bestlaohe/newmsg/Peripheral/inc/ch32v00x.h

/********************************** (C) COPYRIGHT  *******************************
 * File Name          : ch32v00x.h
 * Author             : WCH
 * Version            : V1.0.0
 * Date               : 2024/05/28
 * Description        : CH32V00x Device Peripheral Access Layer Header File.
 *********************************************************************************
 * Copyright (c) 2021 Nanjing Qinheng Microelectronics Co., Ltd.
 * Attention: This software (modified or not) and binary are used for 
 * microcontroller manufactured by Nanjing Qinheng Microelectronics.
 *******************************************************************************/
#ifndef __CH32V00x_H
#define __CH32V00x_H

#ifdef __cplusplus
extern "C" {
#endif

#define HSE_VALUE                 ((uint32_t)24000000) /* Value of the External oscillator in Hz */

/* In the following line adjust the External High Speed oscillator (HSE) Startup Timeout value */
#define HSE_STARTUP_TIMEOUT       ((uint16_t)0x2000) /* Time out for HSE start up */

#define HSI_VALUE                 ((uint32_t)24000000) /* Value of the Internal oscillator in Hz */

/* CH32V00x Standard Peripheral Library version number */
#define __CH32V00x_STDPERIPH_VERSION_MAIN   (0x01) /* [15:8] main version */
#define __CH32V00x_STDPERIPH_VERSION_SUB    (0x09) /* [7:0] sub version */
#define __CH32V00x_STDPERIPH_VERSION        ( (__CH32V00x_STDPERIPH_VERSION_MAIN << 8)\
                                             |(__CH32V00x_STDPERIPH_VERSION_SUB << 0))

/* Interrupt Number Definition, according to the selected device */
typedef enum IRQn
{
    /******  RISC-V Processor Exceptions Numbers *******************************************************/
    NonMaskableInt_IRQn = 2, /* 2 Non Maskable Interrupt                             */
    EXC_IRQn = 3,            /* 3 Exception Interrupt                                */
    SysTicK_IRQn = 12,       /* 12 System timer Interrupt                            */
    Software_IRQn = 14,      /* 14 software Interrupt                                */

    /******  RISC-V specific Interrupt Numbers *********************************************************/
    WWDG_IRQn = 16,          /* Window WatchDog Interrupt                            */
    PVD_IRQn = 17,           /* PVD through EXTI Line detection Interrupt            */
    FLASH_IRQn = 18,         /* FLASH global Interrupt                               */
    RCC_IRQn = 19,           /* RCC global Interrupt                                 */
    EXTI7_0_IRQn = 20,       /* External Line[7:0] Interrupts                        */
    AWU_IRQn = 21,           /* AWU global Interrupt                                 */
    DMA1_Channel1_IRQn = 22, /* DMA1 Channel 1 global Interrupt                      */
    DMA1_Channel2_IRQn = 23, /* DMA1 Channel 2 global Interrupt                      */
    DMA1_Channel3_IRQn = 24, /* DMA1 Channel 3 global Interrupt                      */
    DMA1_Channel4_IRQn = 25, /* DMA1 Channel 4 global Interrupt                      */
    DMA1_Channel5_IRQn = 26, /* DMA1 Channel 5 global Interrupt                      */
    DMA1_Channel6_IRQn = 27, /* DMA1 Channel 6 global Interrupt                      */
    DMA1_Channel7_IRQn = 28, /* DMA1 Channel 7 global Interrupt                      */
    ADC_IRQn = 29,           /* ADC global Interrupt                                 */
    I2C1_EV_IRQn = 30,       /* I2C1 Event Interrupt                                 */
    I2C1_ER_IRQn = 31,       /* I2C1 Error Interrupt                                 */
    USART1_IRQn = 32,        /* USART1 global Interrupt                              */
    SPI1_IRQn = 33,          /* SPI1 global Interrupt                                */
    TIM1_BRK_IRQn = 34,      /* TIM1 Break Interrupt                                 */
    TIM1_UP_IRQn = 35,       /* TIM1 Update Interrupt                                */
    TIM1_TRG_COM_IRQn = 36,  /* TIM1 Trigger and Commutation Interrupt               */
    TIM1_CC_IRQn = 37,       /* TIM1 Capture Compare Interrupt                       */
    TIM2_IRQn = 38,          /* TIM2 global Interrupt                                */

} IRQn_Type;

#define HardFault_IRQn    EXC_IRQn

#include <stdint.h>
#include <core_riscv.h>
#include <system_ch32v00x.h>

/* Standard Peripheral Library old definitions (maintained for legacy purpose) */
#define HSI_Value             HSI_VALUE
#define HSE_Value             HSE_VALUE
#define HSEStartUp_TimeOut    HSE_STARTUP_TIMEOUT

/* Analog to Digital Converter */
typedef struct
{
    __IO uint32_t STATR;
    __IO uint32_t CTLR1;
    __IO uint32_t CTLR2;
    __IO uint32_t SAMPTR1;
    __IO uint32_t SAMPTR2;
    __IO uint32_t IOFR1;
    __IO uint32_t IOFR2;
    __IO uint32_t IOFR3;
    __IO uint32_t IOFR4;
    __IO uint32_t WDHTR;
    __IO uint32_t WDLTR;
    __IO uint32_t RSQR1;
    __IO uint32_t RSQR2;
    __IO uint32_t RSQR3;
    __IO uint32_t ISQR;
    __IO uint32_t IDATAR1;
    __IO uint32_t IDATAR2;
    __IO uint32_t IDATAR3;
    __IO uint32_t IDATAR4;
    __IO uint32_t RDATAR;
    __IO uint32_t DLYR;
} ADC_TypeDef;

/* Debug MCU */
typedef struct
{
    __IO uint32_t CFGR0;
    __IO uint32_t CFGR1;
} DBGMCU_TypeDef;

/* DMA Controller */
typedef struct
{
    __IO uint32_t CFGR;
    __IO uint32_t CNTR;
    __IO uint32_t PADDR;
    __IO uint32_t MADDR;
} DMA_Channel_TypeDef;

typedef struct
{
    __IO uint32_t INTFR;
    __IO uint32_t INTFCR;
} DMA_TypeDef;

/* External Interrupt/Event Controller */
typedef struct
{
    __IO uint32_t INTENR;
    __IO uint32_t EVENR;
    __IO uint32_t RTENR;
    __IO uint32_t FTENR;
    __IO uint32_t SWIEVR;
    __IO uint32_t INTFR;
} EXTI_TypeDef;

/* FLASH Registers */
typedef struct
{
    __IO uint32_t ACTLR;
    __IO uint32_t KEYR;
    __IO uint32_t OBKEYR;
    __IO uint32_t STATR;
    __IO uint32_t CTLR;
    __IO uint32_t ADDR;
    __IO uint32_t RESERVED;
    __IO uint32_t OBR;
    __IO uint32_t WPR;
    __IO uint32_t MODEKEYR;
    __IO uint32_t BOOT_MODEKEYR;
} FLASH_TypeDef;

/* Option Bytes Registers */
typedef struct
{
    __IO uint16_t RDPR;
    __IO uint16_t USER;
    __IO uint16_t Data0;
    __IO uint16_t Data1;
    __IO uint16_t WRPR0;
    __IO uint16_t WRPR1;
} OB_TypeDef;

/* General Purpose I/O */
typedef struct
{
    __IO uint32_t CFGLR;
    uint32_t RESERVED0;
    __IO uint32_t INDR;
    __IO uint32_t OUTDR;
    __IO uint32_t BSHR;
    __IO uint32_t BCR;
    __IO uint32_t LCKR;
} GPIO_TypeDef;

/* Alternate Function I/O */
typedef struct
{
    uint32_t RESERVED0;
    __IO uint32_t PCFR1;
    __IO uint32_t EXTICR;
} AFIO_TypeDef;

/* Inter Integrated Circuit Interface */
typedef struct
{
    __IO uint16_t CTLR1;
    uint16_t      RESERVED0;
    __IO uint16_t CTLR2;
    uint16_t      RESERVED1;
    __IO uint16_t OADDR1;
    uint16_t      RESERVED2;
    __IO uint16_t OADDR2;
    uint16_t      RESERVED3;
    __IO uint16_t DATAR;
    uint16_t      RESERVED4;
    __IO uint16_t STAR1;
    uint16_t      RESERVED5;
    __IO uint16_t STAR2;
    uint16_t      RESERVED6;
    __IO uint16_t CKCFGR;
    uint16_t      RESERVED7;
} I2C_TypeDef;

/* Independent WatchDog */
typedef struct
{
    __IO uint32_t CTLR;
    __IO uint32_t PSCR;
    __IO uint32_t RLDR;
    __IO uint32_t STATR;
} IWDG_TypeDef;

/* Power Control */
typedef struct
{
    __IO uint32_t CTLR;
    __IO uint32_t CSR;
    __IO uint32_t AWUCSR;
    __IO uint32_t AWUWR;
    __IO uint32_t AWUPSC;
} PWR_TypeDef;

/* Reset and Clock Control */
typedef struct
{
    __IO uint32_t CTLR;
    __IO uint32_t CFGR0;
    __IO uint32_t INTR;
    __IO uint32_t APB2PRSTR;
    __IO uint32_t APB1PRSTR;
    __IO uint32_t AHBPCENR;
    __IO uint32_t APB2PCENR;
    __IO uint32_t APB1PCENR;
    __IO uint32_t RESERVED0;
    __IO uint32_t RSTSCKR;
} RCC_TypeDef;

/* Serial Peripheral Interface */
typedef struct
{
    __IO uint16_t CTLR1;
    uint16_t      RESERVED0;
    __IO uint16_t CTLR2;
    uint16_t      RESERVED1;
    __IO uint16_t STATR;
    uint16_t      RESERVED2;
    __IO uint16_t DATAR;
    uint16_t      RESERVED3;
    __IO uint16_t CRCR;
    uint16_t      RESERVED4;
    __IO uint16_t RCRCR;
    uint16_t      RESERVED5;
    __IO uint16_t TCRCR;
    uint16_t      RESERVED6;
    uint32_t      RESERVED7;
    uint32_t      RESERVED8;
    __IO uint16_t HSCR;
    uint16_t      RESERVED9;
} SPI_TypeDef;

/* TIM */
typedef struct
{
    __IO uint16_t CTLR1;
    uint16_t      RESERVED0;
    __IO uint16_t CTLR2;
    uint16_t      RESERVED1;
    __IO uint16_t SMCFGR;
    uint16_t      RESERVED2;
    __IO uint16_t DMAINTENR;
    uint16_t      RESERVED3;
    __IO uint16_t INTFR;
    uint16_t      RESERVED4;
    __IO uint16_t SWEVGR;
    uint16_t      RESERVED5;
    __IO uint16_t CHCTLR1;
    uint16_t      RESERVED6;
    __IO uint16_t CHCTLR2;
    uint16_t      RESERVED7;
    __IO uint16_t CCER;
    uint16_t      RESERVED8;
    __IO uint16_t CNT;
    uint16_t      RESERVED9;
    __IO uint16_t PSC;
    uint16_t      RESERVED10;
    __IO uint16_t ATRLR;
    uint16_t      RESERVED11;
    __IO uint16_t RPTCR;
    uint16_t      RESERVED12;
    __IO uint32_t CH1CVR;
    __IO uint32_t CH2CVR;
    __IO uint32_t CH3CVR;
    __IO uint32_t CH4CVR;
    __IO uint16_t BDTR;
    uint16_t      RESERVED13;
    __IO uint16_t DMACFGR;
    uint16_t      RESERVED14;
    __IO uint16_t DMAADR;
    uint16_t      RESERVED15;
} TIM_TypeDef;

/* Universal Synchronous Asynchronous Receiver Transmitter */
typedef struct
{
    __IO uint16_t STATR;
    uint16_t      RESERVED0;
    __IO uint16_t DATAR;
    uint16_t      RESERVED1;
    __IO uint16_t BRR;
    uint16_t      RESERVED2;
    __IO uint16_t CTLR1;
    uint16_t      RESERVED3;
    __IO uint16_t CTLR2;
    uint16_t      RESERVED4;
    __IO uint16_t CTLR3;
    uint16_t      RESERVED5;
    __IO uint16_t GPR;
    uint16_t      RESERVED6;
} USART_TypeDef;

/* Window WatchDog */
typedef struct
{
    __IO uint32_t CTLR;
    __IO uint32_t CFGR;
    __IO uint32_t STATR;
} WWDG_TypeDef;

/* Enhanced Registers */
typedef struct
{
    __IO uint32_t EXTEN_CTR;
} EXTEN_TypeDef;

/* Peripheral memory map */
#define FLASH_BASE                              ((uint32_t)0x08000000) /* FLASH base address in the alias region */
#define SRAM_BASE                               ((uint32_t)0x20000000) /* SRAM base address in the alias region */
#define PERIPH_BASE                             ((uint32_t)0x40000000) /* Peripheral base address in the alias region */

#define APB1PERIPH_BASE                         (PERIPH_BASE)
#define APB2PERIPH_BASE                         (PERIPH_BASE + 0x10000)
#define AHBPERIPH_BASE                          (PERIPH_BASE + 0x20000)

#define TIM2_BASE                               (APB1PERIPH_BASE + 0x0000)
#define WWDG_BASE                               (APB1PERIPH_BASE + 0x2C00)
#define IWDG_BASE                               (APB1PERIPH_BASE + 0x3000)
#define I2C1_BASE                               (APB1PERIPH_BASE + 0x5400)
#define PWR_BASE                                (APB1PERIPH_BASE + 0x7000)

#define AFIO_BASE                               (APB2PERIPH_BASE + 0x0000)
#define EXTI_BASE                               (APB2PERIPH_BASE + 0x0400)
#define GPIOA_BASE                              (APB2PERIPH_BASE + 0x0800)
#define GPIOC_BASE                              (APB2PERIPH_BASE + 0x1000)
#define GPIOD_BASE                              (APB2PERIPH_BASE + 0x1400)
#define ADC1_BASE                               (APB2PERIPH_BASE + 0x2400)
#define TIM1_BASE                               (APB2PERIPH_BASE + 0x2C00)
#define SPI1_BASE                               (APB2PERIPH_BASE + 0x3000)
#define USART1_BASE                             (APB2PERIPH_BASE + 0x3800)

#define DMA1_BASE                               (AHBPERIPH_BASE + 0x0000)
#define DMA1_Channel1_BASE                      (AHBPERIPH_BASE + 0x0008)
#define DMA1_Channel2_BASE                      (AHBPERIPH_BASE + 0x001C)
#define DMA1_Channel3_BASE                      (AHBPERIPH_BASE + 0x0030)
#define DMA1_Channel4_BASE                      (AHBPERIPH_BASE + 0x0044)
#define DMA1_Channel5_BASE                      (AHBPERIPH_BASE + 0x0058)
#define DMA1_Channel6_BASE                      (AHBPERIPH_BASE + 0x006C)
#define DMA1_Channel7_BASE                      (AHBPERIPH_BASE + 0x0080)
#define RCC_BASE                                (AHBPERIPH_BASE + 0x1000)

#define FLASH_R_BASE                            (AHBPERIPH_BASE + 0x2000) /* Flash registers base address */
#define OB_BASE                                 ((uint32_t)0x1FFFF800)    /* Flash Option Bytes base address */
#define EXTEN_BASE                              ((uint32_t)0x40023800)

#define VENDOR_CFG0_BASE                        ((uint32_t)0x1FFFF7D4)
#define CFG0_PLL_TRIM                           (VENDOR_CFG0_BASE)

/* Peripheral declaration */
#define TIM2                                    ((TIM_TypeDef *)TIM2_BASE)
#define WWDG                                    ((WWDG_TypeDef *)WWDG_BASE)
#define IWDG                                    ((IWDG_TypeDef *)IWDG_BASE)
#define I2C1                                    ((I2C_TypeDef *)I2C1_BASE)
#define PWR                                     ((PWR_TypeDef *)PWR_BASE)
#define AFIO                                    ((AFIO_TypeDef *)AFIO_BASE)
#define EXTI                                    ((EXTI_TypeDef *)EXTI_BASE)
#define GPIOA                                   ((GPIO_TypeDef *)GPIOA_BASE)
#define GPIOC                                   ((GPIO_TypeDef *)GPIOC_BASE)
#define GPIOD                                   ((GPIO_TypeDef *)GPIOD_BASE)
#define ADC1                                    ((ADC_TypeDef *)ADC1_BASE)
#define TIM1                                    ((TIM_TypeDef *)TIM1_BASE)
#define SPI1                                    ((SPI_TypeDef *)SPI1_BASE)
#define USART1                                  ((USART_TypeDef *)USART1_BASE)
#define DMA1                                    ((DMA_TypeDef *)DMA1_BASE)
#define DMA1_Channel1                           ((DMA_Channel_TypeDef *)DMA1_Channel1_BASE)
#define DMA1_Channel2                           ((DMA_Channel_TypeDef *)DMA1_Channel2_BASE)
#define DMA1_Channel3                           ((DMA_Channel_TypeDef *)DMA1_Channel3_BASE)
#define DMA1_Channel4                           ((DMA_Channel_TypeDef *)DMA1_Channel4_BASE)
#define DMA1_Channel5                           ((DMA_Channel_TypeDef *)DMA1_Channel5_BASE)
#define DMA1_Channel6                           ((DMA_Channel_TypeDef *)DMA1_Channel6_BASE)
#define DMA1_Channel7                           ((DMA_Channel_TypeDef *)DMA1_Channel7_BASE)
#define RCC                                     ((RCC_TypeDef *)RCC_BASE)
#define FLASH                                   ((FLASH_TypeDef *)FLASH_R_BASE)
#define OB                                      ((OB_TypeDef *)OB_BASE)
#define EXTEN                                   ((EXTEN_TypeDef *)EXTEN_BASE)

/******************************************************************************/
/*                         Peripheral Registers Bits Definition               */
/******************************************************************************/

/******************************************************************************/
/*                        Analog to Digital Converter                         */
/******************************************************************************/

/********************  Bit definition for ADC_STATR register  ********************/
#define ADC_AWD                                 ((uint8_t)0x01) /* Analog watchdog flag */
#define ADC_EOC                                 ((uint8_t)0x02) /* End of conversion */
#define ADC_JEOC                                ((uint8_t)0x04) /* Injected channel end of conversion */
#define ADC_JSTRT                               ((uint8_t)0x08) /* Injected channel Start flag */
#define ADC_STRT                                ((uint8_t)0x10) /* Regular channel Start flag */

/*******************  Bit definition for ADC_CTLR1 register  ********************/
#define ADC_AWDCH                               ((uint32_t)0x0000001F) /* AWDCH[4:0] bits (Analog watchdog channel select bits) */
#define ADC_AWDCH_0                             ((uint32_t)0x00000001) /* Bit 0 */
#define ADC_AWDCH_1                             ((uint32_t)0x00000002) /* Bit 1 */
#define ADC_AWDCH_2                             ((uint32_t)0x00000004) /* Bit 2 */
#define ADC_AWDCH_3                             ((uint32_t)0x00000008) /* Bit 3 */
#define ADC_AWDCH_4                             ((uint32_t)0x00000010) /* Bit 4 */

#define ADC_EOCIE                               ((uint32_t)0x00000020) /* Interrupt enable for EOC */
#define ADC_AWDIE                               ((uint32_t)0x00000040) /* Analog Watchdog interrupt enable */
#define ADC_JEOCIE                              ((uint32_t)0x00000080) /* Interrupt enable for injected channels */
#define ADC_SCAN                                ((uint32_t)0x00000100) /* Scan mode */
#define ADC_AWDSGL                              ((uint32_t)0x00000200) /* Enable the watchdog on a single channel in scan mode */
#define ADC_JAUTO                               ((uint32_t)0x00000400) /* Automatic injected group conversion */
#define ADC_DISCEN                              ((uint32_t)0x00000800) /* Discontinuous mode on regular channels */
#define ADC_JDISCEN                             ((uint32_t)0x00001000) /* Discontinuous mode on injected channels */

#define ADC_DISCNUM                             ((uint32_t)0x0000E000) /* DISCNUM[2:0] bits (Discontinuous mode channel count) */
#define ADC_DISCNUM_0                           ((uint32_t)0x00002000) /* Bit 0 */
#define ADC_DISCNUM_1                           ((uint32_t)0x00004000) /* Bit 1 */
#define ADC_DISCNUM_2                           ((uint32_t)0x00008000) /* Bit 2 */

#define ADC_JAWDEN                              ((uint32_t)0x00400000) /* Analog watchdog enable on injected channels */
#define ADC_AWDEN                               ((uint32_t)0x00800000) /* Analog watchdog enable on regular channels */
#define ADC_CALVOLSELECT                        ((uint32_t)0x06000000)
#define ADC_CALVOLSELECT_0                      ((uint32_t)0x02000000)
#define ADC_CALVOLSELECT_1                      ((uint32_t)0x04000000)

/*******************  Bit definition for ADC_CTLR2 register  ********************/
#define ADC_ADON                                ((uint32_t)0x00000001) /* A/D Converter ON / OFF */
#define ADC_CONT                                ((uint32_t)0x00000002) /* Continuous Conversion */
#define ADC_CAL                                 ((uint32_t)0x00000004) /* A/D Calibration */
#define ADC_RSTCAL                              ((uint32_t)0x00000008) /* Reset Calibration */
#define ADC_DMA                                 ((uint32_t)0x00000100) /* Direct Memory access mode */
#define ADC_ALIGN                               ((uint32_t)0x00000800) /* Data Alignment */

#define ADC_JEXTSEL                             ((uint32_t)0x00007000) /* JEXTSEL[2:0] bits (External event select for injected group) */
#define ADC_JEXTSEL_0                           ((uint32_t)0x00001000) /* Bit 0 */
#define ADC_JEXTSEL_1                           ((uint32_t)0x00002000) /* Bit 1 */
#define ADC_JEXTSEL_2                           ((uint32_t)0x00004000) /* Bit 2 */

#define ADC_JEXTTRIG                            ((uint32_t)0x00008000) /* External Trigger Conversion mode for injected channels */

#define ADC_EXTSEL                              ((uint32_t)0x000E0000) /* EXTSEL[2:0] bits (External Event Select for regular group) */
#define ADC_EXTSEL_0                            ((uint32_t)0x00020000) /* Bit 0 */
#define ADC_EXTSEL_1                            ((uint32_t)0x00040000) /* Bit 1 */
#define ADC_EXTSEL_2                            ((uint32_t)0x00080000) /* Bit 2 */

#define ADC_EXTTRIG                             ((uint32_t)0x00100000) /* External Trigger Conversion mode for regular channels */
#define ADC_JSWSTART                            ((uint32_t)0x00200000) /* Start Conversion of injected channels */
#define ADC_SWSTART                             ((uint32_t)0x00400000) /* Start Conversion of regular channels */

/******************  Bit definition for ADC_SAMPTR1 register  *******************/
#define ADC_SMP10                               ((uint32_t)0x00000007) /* SMP10[2:0] bits (Channel 10 Sample time selection) */
#define ADC_SMP10_0                             ((uint32_t)0x00000001) /* Bit 0 */
#define ADC_SMP10_1                             ((uint32_t)0x00000002) /* Bit 1 */
#define ADC_SMP10_2                             ((uint32_t)0x00000004) /* Bit 2 */

#define ADC_SMP11                               ((uint32_t)0x00000038) /* SMP11[2:0] bits (Channel 11 Sample time selection) */
#define ADC_SMP11_0                             ((uint32_t)0x00000008) /* Bit 0 */
#define ADC_SMP11_1                             ((uint32_t)0x00000010) /* Bit 1 */
#define ADC_SMP11_2                             ((uint32_t)0x00000020) /* Bit 2 */

#define ADC_SMP12                               ((uint32_t)0x000001C0) /* SMP12[2:0] bits (Channel 12 Sample time selection) */
#define ADC_SMP12_0                             ((uint32_t)0x00000040) /* Bit 0 */
#define ADC_SMP12_1                             ((uint32_t)0x00000080) /* Bit 1 */
#define ADC_SMP12_2                             ((uint32_t)0x00000100) /* Bit 2 */

#define ADC_SMP13                               ((uint32_t)0x00000E00) /* SMP13[2:0] bits (Channel 13 Sample time selection) */
#define ADC_SMP13_0                             ((uint32_t)0x00000200) /* Bit 0 */
#define ADC_SMP13_1                             ((uint32_t)0x00000400) /* Bit 1 */
#define ADC_SMP13_2                             ((uint32_t)0x00000800) /* Bit 2 */

#define ADC_SMP14                               ((uint32_t)0x00007000) /* SMP14[2:0] bits (Channel 14 Sample time selection) */
#define ADC_SMP14_0                             ((uint32_t)0x00001000) /* Bit 0 */
#define ADC_SMP14_1                             ((uint32_t)0x00002000) /* Bit 1 */
#define ADC_SMP14_2                             ((uint32_t)0x00004000) /* Bit 2 */

#define ADC_SMP15                               ((uint32_t)0x00038000) /* SMP15[2:0] bits (Channel 15 Sample time selection) */
#define ADC_SMP15_0                             ((uint32_t)0x00008000) /* Bit 0 */
#define ADC_SMP15_1                             ((uint32_t)0x00010000) /* Bit 1 */
#define ADC_SMP15_2                             ((uint32_t)0x00020000) /* Bit 2 */

/******************  Bit definition for ADC_SAMPTR2 register  *******************/
#define ADC_SMP0                                ((uint32_t)0x00000007) /* SMP0[2:0] bits (Channel 0 Sample time selection) */
#define ADC_SMP0_0                              ((uint32_t)0x00000001) /* Bit 0 */
#define ADC_SMP0_1                              ((uint32_t)0x00000002) /* Bit 1 */
#define ADC_SMP0_2                              ((uint32_t)0x00000004) /* Bit 2 */

#define ADC_SMP1                                ((uint32_t)0x00000038) /* SMP1[2:0] bits (Channel 1 Sample time selection) */
#define ADC_SMP1_0                              ((uint32_t)0x00000008) /* Bit 0 */
#define ADC_SMP1_1                              ((uint32_t)0x00000010) /* Bit 1 */
#define ADC_SMP1_2                              ((uint32_t)0x00000020) /* Bit 2 */

#define ADC_SMP2                                ((uint32_t)0x000001C0) /* SMP2[2:0] bits (Channel 2 Sample time selection) */
#define ADC_SMP2_0                              ((uint32_t)0x00000040) /* Bit 0 */
#define ADC_SMP2_1                              ((uint32_t)0x00000080) /* Bit 1 */
#define ADC_SMP2_2                              ((uint32_t)0x00000100) /* Bit 2 */

#define ADC_SMP3                                ((uint32_t)0x00000E00) /* SMP3[2:0] bits (Channel 3 Sample time selection) */
#define ADC_SMP3_0                              ((uint32_t)0x00000200) /* Bit 0 */
#define ADC_SMP3_1                              ((uint32_t)0x00000400) /* Bit 1 */
#define ADC_SMP3_2                              ((uint32_t)0x00000800) /* Bit 2 */

#define ADC_SMP4                                ((uint32_t)0x00007000) /* SMP4[2:0] bits (Channel 4 Sample time selection) */
#define ADC_SMP4_0                              ((uint32_t)0x00001000) /* Bit 0 */
#define ADC_SMP4_1                              ((uint32_t)0x00002000) /* Bit 1 */
#define ADC_SMP4_2                              ((uint32_t)0x00004000) /* Bit 2 */

#define ADC_SMP5                                ((uint32_t)0x00038000) /* SMP5[2:0] bits (Channel 5 Sample time selection) */
#define ADC_SMP5_0                              ((uint32_t)0x00008000) /* Bit 0 */
#define ADC_SMP5_1                              ((uint32_t)0x00010000) /* Bit 1 */
#define ADC_SMP5_2                              ((uint32_t)0x00020000) /* Bit 2 */

#define ADC_SMP6                                ((uint32_t)0x001C0000) /* SMP6[2:0] bits (Channel 6 Sample time selection) */
#define ADC_SMP6_0                              ((uint32_t)0x00040000) /* Bit 0 */
#define ADC_SMP6_1                              ((uint32_t)0x00080000) /* Bit 1 */
#define ADC_SMP6_2                              ((uint32_t)0x00100000) /* Bit 2 */

#define ADC_SMP7                                ((uint32_t)0x00E00000) /* SMP7[2:0] bits (Channel 7 Sample time selection) */
#define ADC_SMP7_0                              ((uint32_t)0x00200000) /* Bit 0 */
#define ADC_SMP7_1                              ((uint32_t)0x00400000) /* Bit 1 */
#define ADC_SMP7_2                              ((uint32_t)0x00800000) /* Bit 2 */

#define ADC_SMP8                                ((uint32_t)0x07000000) /* SMP8[2:0] bits (Channel 8 Sample time selection) */
#define ADC_SMP8_0                              ((uint32_t)0x01000000) /* Bit 0 */
#define ADC_SMP8_1                              ((uint32_t)0x02000000) /* Bit 1 */
#define ADC_SMP8_2                              ((uint32_t)0x04000000) /* Bit 2 */

#define ADC_SMP9                                ((uint32_t)0x38000000) /* SMP9[2:0] bits (Channel 9 Sample time selection) */
#define ADC_SMP9_0                              ((uint32_t)0x08000000) /* Bit 0 */
#define ADC_SMP9_1                              ((uint32_t)0x10000000) /* Bit 1 */
#define ADC_SMP9_2                              ((uint32_t)0x20000000) /* Bit 2 */

/******************  Bit definition for ADC_IOFR1 register  *******************/
#define ADC_JOFFSET1                            ((uint16_t)0x03FF) /* Data offset for injected channel 1 */

/******************  Bit definition for ADC_IOFR2 register  *******************/
#define ADC_JOFFSET2                            ((uint16_t)0x03FF) /* Data offset for injected channel 2 */

/******************  Bit definition for ADC_IOFR3 register  *******************/
#define ADC_JOFFSET3                            ((uint16_t)0x03FF) /* Data offset for injected channel 3 */

/******************  Bit definition for ADC_IOFR4 register  *******************/
#define ADC_JOFFSET4                            ((uint16_t)0x03FF) /* Data offset for injected channel 4 */

/*******************  Bit definition for ADC_WDHTR register  ********************/
#define ADC_HT                                  ((uint16_t)0x03FF) /* Analog watchdog high threshold */

/*******************  Bit definition for ADC_WDLTR register  ********************/
#define ADC_LT                                  ((uint16_t)0x03FF) /* Analog watchdog low threshold */

/*******************  Bit definition for ADC_RSQR1 register  *******************/
#define ADC_SQ13                                ((uint32_t)0x0000001F) /* SQ13[4:0] bits (13th conversion in regular sequence) */
#define ADC_SQ13_0                              ((uint32_t)0x00000001) /* Bit 0 */
#define ADC_SQ13_1                              ((uint32_t)0x00000002) /* Bit 1 */
#define ADC_SQ13_2                              ((uint32_t)0x00000004) /* Bit 2 */
#define ADC_SQ13_3                              ((uint32_t)0x00000008) /* Bit 3 */
#define ADC_SQ13_4                              ((uint32_t)0x00000010) /* Bit 4 */

#define ADC_SQ14                                ((uint32_t)0x000003E0) /* SQ14[4:0] bits (14th conversion in regular sequence) */
#define ADC_SQ14_0                              ((uint32_t)0x00000020) /* Bit 0 */
#define ADC_SQ14_1                              ((uint32_t)0x00000040) /* Bit 1 */
#define ADC_SQ14_2                              ((uint32_t)0x00000080) /* Bit 2 */
#define ADC_SQ14_3                              ((uint32_t)0x00000100) /* Bit 3 */
#define ADC_SQ14_4                              ((uint32_t)0x00000200) /* Bit 4 */

#define ADC_SQ15                                ((uint32_t)0x00007C00) /* SQ15[4:0] bits (15th conversion in regular sequence) */
#define ADC_SQ15_0                              ((uint32_t)0x00000400) /* Bit 0 */
#define ADC_SQ15_1                              ((uint32_t)0x00000800) /* Bit 1 */
#define ADC_SQ15_2                              ((uint32_t)0x00001000) /* Bit 2 */
#define ADC_SQ15_3                              ((uint32_t)0x00002000) /* Bit 3 */
#define ADC_SQ15_4                              ((uint32_t)0x00004000) /* Bit 4 */

#define ADC_SQ16                                ((uint32_t)0x000F8000) /* SQ16[4:0] bits (16th conversion in regular sequence) */
#define ADC_SQ16_0                              ((uint32_t)0x00008000) /* Bit 0 */
#define ADC_SQ16_1                              ((uint32_t)0x00010000) /* Bit 1 */
#define ADC_SQ16_2                              ((uint32_t)0x00020000) /* Bit 2 */
#define ADC_SQ16_3                              ((uint32_t)0x00040000) /* Bit 3 */
#define ADC_SQ16_4                              ((uint32_t)0x00080000) /* Bit 4 */

#define ADC_L                                   ((uint32_t)0x00F00000) /* L[3:0] bits (Regular channel sequence length) */
#define ADC_L_0                                 ((uint32_t)0x00100000) /* Bit 0 */
#define ADC_L_1                                 ((uint32_t)0x00200000) /* Bit 1 */
#define ADC_L_2                                 ((uint32_t)0x00400000) /* Bit 2 */
#define ADC_L_3                                 ((uint32_t)0x00800000) /* Bit 3 */

/*******************  Bit definition for ADC_RSQR2 register  *******************/
#define ADC_SQ7                                 ((uint32_t)0x0000001F) /* SQ7[4:0] bits (7th conversion in regular sequence) */
#define ADC_SQ7_0                               ((uint32_t)0x00000001) /* Bit 0 */
#define ADC_SQ7_1                               ((uint32_t)0x00000002) /* Bit 1 */
#define ADC_SQ7_2                               ((uint32_t)0x00000004) /* Bit 2 */
#define ADC_SQ7_3                               ((uint32_t)0x00000008) /* Bit 3 */
#define ADC_SQ7_4                               ((uint32_t)0x00000010) /* Bit 4 */

#define ADC_SQ8                                 ((uint32_t)0x000003E0) /* SQ8[4:0] bits (8th conversion in regular sequence) */
#define ADC_SQ8_0                               ((uint32_t)0x00000020) /* Bit 0 */
#define ADC_SQ8_1                               ((uint32_t)0x00000040) /* Bit 1 */
#define ADC_SQ8_2                               ((uint32_t)0x00000080) /* Bit 2 */
#define ADC_SQ8_3                               ((uint32_t)0x00000100) /* Bit 3 */
#define ADC_SQ8_4                               ((uint32_t)0x00000200) /* Bit 4 */

#define ADC_SQ9                                 ((uint32_t)0x00007C00) /* SQ9[4:0] bits (9th conversion in regular sequence) */
#define ADC_SQ9_0                               ((uint32_t)0x00000400) /* Bit 0 */
#define ADC_SQ9_1                               ((uint32_t)0x00000800) /* Bit 1 */
#define ADC_SQ9_2                               ((uint32_t)0x00001000) /* Bit 2 */
#define ADC_SQ9_3                               ((uint32_t)0x00002000) /* Bit 3 */
#define ADC_SQ9_4                               ((uint32_t)0x00004000) /* Bit 4 */

#define ADC_SQ10                                ((uint32_t)0x000F8000) /* SQ10[4:0] bits (10th conversion in regular sequence) */
#define ADC_SQ10_0                              ((uint32_t)0x00008000) /* Bit 0 */
#define ADC_SQ10_1                              ((uint32_t)0x00010000) /* Bit 1 */
#define ADC_SQ10_2                              ((uint32_t)0x00020000) /* Bit 2 */
#define ADC_SQ10_3                              ((uint32_t)0x00040000) /* Bit 3 */
#define ADC_SQ10_4                              ((uint32_t)0x00080000) /* Bit 4 */

#define ADC_SQ11                                ((uint32_t)0x01F00000) /* SQ11[4:0] bits (11th conversion in regular sequence) */
#define ADC_SQ11_0                              ((uint32_t)0x00100000) /* Bit 0 */
#define ADC_SQ11_1                              ((uint32_t)0x00200000) /* Bit 1 */
#define ADC_SQ11_2                              ((uint32_t)0x00400000) /* Bit 2 */
#define ADC_SQ11_3                              ((uint32_t)0x00800000) /* Bit 3 */
#define ADC_SQ11_4                              ((uint32_t)0x01000000) /* Bit 4 */

#define ADC_SQ12                                ((uint32_t)0x3E000000) /* SQ12[4:0] bits (12th conversion in regular sequence) */
#define ADC_SQ12_0                              ((uint32_t)0x02000000) /* Bit 0 */
#define ADC_SQ12_1                              ((uint32_t)0x04000000) /* Bit 1 */
#define ADC_SQ12_2                              ((uint32_t)0x08000000) /* Bit 2 */
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
#define ADC_JSQ1_2                              ((uint32_t)0x00000004) /* Bit 2 */
#define ADC_JSQ1_3                              ((uint32_t)0x00000008) /* Bit 3 */
#define ADC_JSQ1_4                              ((uint32_t)0x00000010) /* Bit 4 */

#define ADC_JSQ2                                ((uint32_t)0x000003E0) /* JSQ2[4:0] bits (2nd conversion in injected sequence) */
#define ADC_JSQ2_0                              ((uint32_t)0x00000020) /* Bit 0 */
#define ADC_JSQ2_1                              ((uint32_t)0x00000040) /* Bit 1 */
#define ADC_JSQ2_2                              ((uint32_t)0x00000080) /* Bit 2 */
#define ADC_JSQ2_3                              ((uint32_t)0x00000100) /* Bit 3 */
#define ADC_JSQ2_4                              ((uint32_t)0x00000200) /* Bit 4 */

#define ADC_JSQ3                                ((uint32_t)0x00007C00) /* JSQ3[4:0] bits (3rd conversion in injected sequence) */
#define ADC_JSQ3_0                              ((uint32_t)0x00000400) /* Bit 0 */
#define ADC_JSQ3_1                              ((uint32_t)0x00000800) /* Bit 1 */
#define ADC_JSQ3_2                              ((uint32_t)0x00001000) /* Bit 2 */
#define ADC_JSQ3_3                              ((uint32_t)0x00002000) /* Bit 3 */
#define ADC_JSQ3_4                              ((uint32_t)0x00004000) /* Bit 4 */

#define ADC_JSQ4                                ((uint32_t)0x000F8000) /* JSQ4[4:0] bits (4th conversion in injected sequence) */
#define ADC_JSQ4_0                              ((uint32_t)0x00008000) /* Bit 0 */
#define ADC_JSQ4_1                              ((uint32_t)0x00010000) /* Bit 1 */
#define ADC_JSQ4_2                              ((uint32_t)0x00020000) /* Bit 2 */
#define ADC_JSQ4_3                              ((uint32_t)0x00040000) /* Bit 3 */
#define ADC_JSQ4_4                              ((uint32_t)0x00080000) /* Bit 4 */

#define ADC_JL                                  ((uint32_t)0x00300000) /* JL[1:0] bits (Injected Sequence length) */
#define ADC_JL_0                                ((uint32_t)0x00100000) /* Bit 0 */
#define ADC_JL_1                                ((uint32_t)0x00200000) /* Bit 1 */

/*******************  Bit definition for ADC_IDATAR1 register  *******************/
#define ADC_IDATAR1_JDATA                       ((uint16_t)0xFFFF) /* Injected data */

/*******************  Bit definition for ADC_IDATAR2 register  *******************/
#define ADC_IDATAR2_JDATA                       ((uint16_t)0xFFFF) /* Injected data */

/*******************  Bit definition for ADC_IDATAR3 register  *******************/
#define ADC_IDATAR3_JDATA                       ((uint16_t)0xFFFF) /* Injected data */

/*******************  Bit definition for ADC_IDATAR4 register  *******************/
#define ADC_IDATAR4_JDATA                       ((uint16_t)0xFFFF) /* Injected data */

/********************  Bit definition for ADC_RDATAR register  ********************/
#define ADC_RDATAR_DATA                         ((uint32_t)0xFFFFFFFF) /* Regular data */

/********************  Bit definition for ADC_DLYR register  ********************/
#define ADC_DLYR_DLYVLU                         ((uint32_t)0x1FF) 
#define ADC_DLYR_DLYSRC                         ((uint32_t)0x200) 

/******************************************************************************/
/*                             DMA Controller                                 */
/******************************************************************************/

/*******************  Bit definition for DMA_INTFR register  ********************/
#define DMA_GIF1                                ((uint32_t)0x00000001) /* Channel 1 Global interrupt flag */
#define DMA_TCIF1                               ((uint32_t)0x00000002) /* Channel 1 Transfer Complete flag */
#define DMA_HTIF1                               ((uint32_t)0x00000004) /* Channel 1 Half Transfer flag */
#define DMA_TEIF1                               ((uint32_t)0x00000008) /* Channel 1 Transfer Error flag */
#define DMA_GIF2                                ((uint32_t)0x00000010) /* Channel 2 Global interrupt flag */
#define DMA_TCIF2                               ((uint32_t)0x00000020) /* Channel 2 Transfer Complete flag */
#define DMA_HTIF2                               ((uint32_t)0x00000040) /* Channel 2 Half Transfer flag */
#define DMA_TEIF2                               ((uint32_t)0x00000080) /* Channel 2 Transfer Error flag */
#define DMA_GIF3                                ((uint32_t)0x00000100) /* Channel 3 Global interrupt flag */
#define DMA_TCIF3                               ((uint32_t)0x00000200) /* Channel 3 Transfer Complete flag */
#define DMA_HTIF3                               ((uint32_t)0x00000400) /* Channel 3 Half Transfer flag */
#define DMA_TEIF3                               ((uint32_t)0x00000800) /* Channel 3 Transfer Error flag */
#define DMA_GIF4                                ((uint32_t)0x00001000) /* Channel 4 Global interrupt flag */
#define DMA_TCIF4                               ((uint32_t)0x00002000) /* Channel 4 Transfer Complete flag */
#define DMA_HTIF4                               ((uint32_t)0x00004000) /* Channel 4 Half Transfer flag */
#define DMA_TEIF4                               ((uint32_t)0x00008000) /* Channel 4 Transfer Error flag */
#define DMA_GIF5                                ((uint32_t)0x00010000) /* Channel 5 Global interrupt flag */
#define DMA_TCIF5                               ((uint32_t)0x00020000) /* Channel 5 Transfer Complete flag */
#define DMA_HTIF5                               ((uint32_t)0x00040000) /* Channel 5 Half Transfer flag */
#define DMA_TEIF5                               ((uint32_t)0x00080000) /* Channel 5 Transfer Error flag */
#define DMA_GIF6                                ((uint32_t)0x00100000) /* Channel 6 Global interrupt flag */
#define DMA_TCIF6                               ((uint32_t)0x00200000) /* Channel 6 Transfer Complete flag */
#define DMA_HTIF6                               ((uint32_t)0x00400000) /* Channel 6 Half Transfer flag */
#define DMA_TEIF6                               ((uint32_t)0x00800000) /* Channel 6 Transfer Error flag */
#define DMA_GIF7                                ((uint32_t)0x01000000) /* Channel 7 Global interrupt flag */
#define DMA_TCIF7                               ((uint32_t)0x02000000) /* Channel 7 Transfer Complete flag */
#define DMA_HTIF7                               ((uint32_t)0x04000000) /* Channel 7 Half Transfer flag */
#define DMA_TEIF7                               ((uint32_t)0x08000000) /* Channel 7 Transfer Error flag */

/*******************  Bit definition for DMA_INTFCR register  *******************/
#define DMA_CGIF1                               ((uint32_t)0x00000001) /* Channel 1 Global interrupt clear */
#define DMA_CTCIF1                              ((uint32_t)0x00000002) /* Channel 1 Transfer Complete clear */
#define DMA_CHTIF1                              ((uint32_t)0x00000004) /* Channel 1 Half Transfer clear */
#define DMA_CTEIF1                              ((uint32_t)0x00000008) /* Channel 1 Transfer Error clear */
#define DMA_CGIF2                               ((uint32_t)0x00000010) /* Channel 2 Global interrupt clear */
#define DMA_CTCIF2                              ((uint32_t)0x00000020) /* Channel 2 Transfer Complete clear */
#define DMA_CHTIF2                              ((uint32_t)0x00000040) /* Channel 2 Half Transfer clear */
#define DMA_CTEIF2                              ((uint32_t)0x00000080) /* Channel 2 Transfer Error clear */
#define DMA_CGIF3                               ((uint32_t)0x00000100) /* Channel 3 Global interrupt clear */
#define DMA_CTCIF3                              ((uint32_t)0x00000200) /* Channel 3 Transfer Complete clear */
#define DMA_CHTIF3                              ((uint32_t)0x00000400) /* Channel 3 Half Transfer clear */
#define DMA_CTEIF3                              ((uint32_t)0x00000800) /* Channel 3 Transfer Error clear */
#define DMA_CGIF4                               ((uint32_t)0x00001000) /* Channel 4 Global interrupt clear */
#define DMA_CTCIF4                              ((uint32_t)0x00002000) /* Channel 4 Transfer Complete clear */
#define DMA_CHTIF4                              ((uint32_t)0x00004000) /* Channel 4 Half Transfer clear */
#define DMA_CTEIF4                              ((uint32_t)0x00008000) /* Channel 4 Transfer Error clear */
#define DMA_CGIF5                               ((uint32_t)0x00010000) /* Channel 5 Global interrupt clear */
#define DMA_CTCIF5                              ((uint32_t)0x00020000) /* Channel 5 Transfer Complete clear */
#define DMA_CHTIF5                              ((uint32_t)0x00040000) /* Channel 5 Half Transfer clear */
#define DMA_CTEIF5                              ((uint32_t)0x00080000) /* Channel 5 Transfer Error clear */
#define DMA_CGIF6                               ((uint32_t)0x00100000) /* Channel 6 Global interrupt clear */
#define DMA_CTCIF6                              ((uint32_t)0x00200000) /* Channel 6 Transfer Complete clear */
#define DMA_CHTIF6                              ((uint32_t)0x00400000) /* Channel 6 Half Transfer clear */
#define DMA_CTEIF6                              ((uint32_t)0x00800000) /* Channel 6 Transfer Error clear */
#define DMA_CGIF7                               ((uint32_t)0x01000000) /* Channel 7 Global interrupt clear */
#define DMA_CTCIF7                              ((uint32_t)0x02000000) /* Channel 7 Transfer Complete clear */
#define DMA_CHTIF7                              ((uint32_t)0x04000000) /* Channel 7 Half Transfer clear */
#define DMA_CTEIF7                              ((uint32_t)0x08000000) /* Channel 7 Transfer Error clear */

/*******************  Bit definition for DMA_CFGR1 register  *******************/
#define DMA_CFGR1_EN                            ((uint16_t)0x0001) /* Channel enable*/
#define DMA_CFGR1_TCIE                          ((uint16_t)0x0002) /* Transfer complete interrupt enable */
#define DMA_CFGR1_HTIE                          ((uint16_t)0x0004) /* Half Transfer interrupt enable */
#define DMA_CFGR1_TEIE                          ((uint16_t)0x0008) /* Transfer error interrupt enable */
#define DMA_CFGR1_DIR                           ((uint16_t)0x0010) /* Data transfer direction */
#define DMA_CFGR1_CIRC                          ((uint16_t)0x0020) /* Circular mode */
#define DMA_CFGR1_PINC                          ((uint16_t)0x0040) /* Peripheral increment mode */
#define DMA_CFGR1_MINC                          ((uint16_t)0x0080) /* Memory increment mode */

#define DMA_CFGR1_PSIZE                         ((uint16_t)0x0300) /* PSIZE[1:0] bits (Peripheral size) */
#define DMA_CFGR1_PSIZE_0                       ((uint16_t)0x0100) /* Bit 0 */
#define DMA_CFGR1_PSIZE_1                       ((uint16_t)0x0200) /* Bit 1 */

#define DMA_CFGR1_MSIZE                         ((uint16_t)0x0C00) /* MSIZE[1:0] bits (Memory size) */
#define DMA_CFGR1_MSIZE_0                       ((uint16_t)0x0400) /* Bit 0 */
#define DMA_CFGR1_MSIZE_1                       ((uint16_t)0x0800) /* Bit 1 */

#define DMA_CFGR1_PL                            ((uint16_t)0x3000) /* PL[1:0] bits(Channel Priority level) */
#define DMA_CFGR1_PL_0                          ((uint16_t)0x1000) /* Bit 0 */
#define DMA_CFGR1_PL_1                          ((uint16_t)0x2000) /* Bit 1 */

#define DMA_CFGR1_MEM2MEM                       ((uint16_t)0x4000) /* Memory to memory mode */

/*******************  Bit definition for DMA_CFGR2 register  *******************/
#define DMA_CFGR2_EN                            ((uint16_t)0x0001) /* Channel enable */
#define DMA_CFGR2_TCIE                          ((uint16_t)0x0002) /* Transfer complete interrupt enable */
#define DMA_CFGR2_HTIE                          ((uint16_t)0x0004) /* Half Transfer interrupt enable */
#define DMA_CFGR2_TEIE                          ((uint16_t)0x0008) /* Transfer error interrupt enable */
#define DMA_CFGR2_DIR                           ((uint16_t)0x0010) /* Data transfer direction */
#define DMA_CFGR2_CIRC                          ((uint16_t)0x0020) /* Circular mode */
#define DMA_CFGR2_PINC                          ((uint16_t)0x0040) /* Peripheral increment mode */
#define DMA_CFGR2_MINC                          ((uint16_t)0x0080) /* Memory increment mode */

#define DMA_CFGR2_PSIZE                         ((uint16_t)0x0300) /* PSIZE[1:0] bits (Peripheral size) */
#define DMA_CFGR2_PSIZE_0                       ((uint16_t)0x0100) /* Bit 0 */
#define DMA_CFGR2_PSIZE_1                       ((uint16_t)0x0200) /* Bit 1 */

#define DMA_CFGR2_MSIZE                         ((uint16_t)0x0C00) /* MSIZE[1:0] bits (Memory size) */
#define DMA_CFGR2_MSIZE_0                       ((uint16_t)0x0400) /* Bit 0 */
#define DMA_CFGR2_MSIZE_1                       ((uint16_t)0x0800) /* Bit 1 */

#define DMA_CFGR2_PL                            ((uint16_t)0x3000) /* PL[1:0] bits (Channel Priority level) */
#define DMA_CFGR2_PL_0                          ((uint16_t)0x1000) /* Bit 0 */
#define DMA_CFGR2_PL_1                          ((uint16_t)0x2000) /* Bit 1 */

#define DMA_CFGR2_MEM2MEM                       ((uint16_t)0x4000) /* Memory to memory mode */

/*******************  Bit definition for DMA_CFGR3 register  *******************/
#define DMA_CFGR3_EN                            ((uint16_t)0x0001) /* Channel enable */
#define DMA_CFGR3_TCIE                          ((uint16_t)0x0002) /* Transfer complete interrupt enable */
#define DMA_CFGR3_HTIE                          ((uint16_t)0x0004) /* Half Transfer interrupt enable */
#define DMA_CFGR3_TEIE                          ((uint16_t)0x0008) /* Transfer error interrupt enable */
#define DMA_CFGR3_DIR                           ((uint16_t)0x0010) /* Data transfer direction */
#define DMA_CFGR3_CIRC                          ((uint16_t)0x0020) /* Circular mode */
#define DMA_CFGR3_PINC                          ((uint16_t)0x0040) /* Peripheral increment mode */
#define DMA_CFGR3_MINC                          ((uint16_t)0x0080) /* Memory increment mode */

#define DMA_CFGR3_PSIZE                         ((uint16_t)0x0300) /* PSIZE[1:0] bits (Peripheral size) */
#define DMA_CFGR3_PSIZE_0                       ((uint16_t)0x0100) /* Bit 0 */
#define DMA_CFGR3_PSIZE_1                       ((uint16_t)0x0200) /* Bit 1 */

#define DMA_CFGR3_MSIZE                         ((uint16_t)0x0C00) /* MSIZE[1:0] bits (Memory size) */
#define DMA_CFGR3_MSIZE_0                       ((uint16_t)0x0400) /* Bit 0 */
#define DMA_CFGR3_MSIZE_1                       ((uint16_t)0x0800) /* Bit 1 */

#define DMA_CFGR3_PL                            ((uint16_t)0x3000) /* PL[1:0] bits (Channel Priority level) */
#define DMA_CFGR3_PL_0                          ((uint16_t)0x1000) /* Bit 0 */
#define DMA_CFGR3_PL_1                          ((uint16_t)0x2000) /* Bit 1 */

#define DMA_CFGR3_MEM2MEM                       ((uint16_t)0x4000) /* Memory to memory mode */

/*******************  Bit definition for DMA_CFG4 register  *******************/
#define DMA_CFG4_EN                             ((uint16_t)0x0001) /* Channel enable */
#define DMA_CFG4_TCIE                           ((uint16_t)0x0002) /* Transfer complete interrupt enable */
#define DMA_CFG4_HTIE                           ((uint16_t)0x0004) /* Half Transfer interrupt enable */
#define DMA_CFG4_TEIE                           ((uint16_t)0x0008) /* Transfer error interrupt enable */
#define DMA_CFG4_DIR                            ((uint16_t)0x0010) /* Data transfer direction */
#define DMA_CFG4_CIRC                           ((uint16_t)0x0020) /* Circular mode */
#define DMA_CFG4_PINC                           ((uint16_t)0x0040) /* Peripheral increment mode */
#define DMA_CFG4_MINC                           ((uint16_t)0x0080) /* Memory increment mode */

#define DMA_CFG4_PSIZE                          ((uint16_t)0x0300) /* PSIZE[1:0] bits (Peripheral size) */
#define DMA_CFG4_PSIZE_0                        ((uint16_t)0x0100) /* Bit 0 */
#define DMA_CFG4_PSIZE_1                        ((uint16_t)0x0200) /* Bit 1 */

#define DMA_CFG4_MSIZE                          ((uint16_t)0x0C00) /* MSIZE[1:0] bits (Memory size) */
#define DMA_CFG4_MSIZE_0                        ((uint16_t)0x0400) /* Bit 0 */
#define DMA_CFG4_MSIZE_1                        ((uint16_t)0x0800) /* Bit 1 */

#define DMA_CFG4_PL                             ((uint16_t)0x3000) /* PL[1:0] bits (Channel Priority level) */
#define DMA_CFG4_PL_0                           ((uint16_t)0x1000) /* Bit 0 */
#define DMA_CFG4_PL_1                           ((uint16_t)0x2000) /* Bit 1 */

#define DMA_CFG4_MEM2MEM                        ((uint16_t)0x4000) /* Memory to memory mode */

/******************  Bit definition for DMA_CFG5 register  *******************/
#define DMA_CFG5_EN                             ((uint16_t)0x0001) /* Channel enable */
#define DMA_CFG5_TCIE                           ((uint16_t)0x0002) /* Transfer complete interrupt enable */
#define DMA_CFG5_HTIE                           ((uint16_t)0x0004) /* Half Transfer interrupt enable */
#define DMA_CFG5_TEIE                           ((uint16_t)0x0008) /* Transfer error interrupt enable */
#define DMA_CFG5_DIR                            ((uint16_t)0x0010) /* Data transfer direction */
#define DMA_CFG5_CIRC                           ((uint16_t)0x0020) /* Circular mode */
#define DMA_CFG5_PINC                           ((uint16_t)0x0040) /* Peripheral increment mode */
#define DMA_CFG5_MINC                           ((uint16_t)0x0080) /* Memory increment mode */

#define DMA_CFG5_PSIZE                          ((uint16_t)0x0300) /* PSIZE[1:0] bits (Peripheral size) */
#define DMA_CFG5_PSIZE_0                        ((uint16_t)0x0100) /* Bit 0 */
#define DMA_CFG5_PSIZE_1                        ((uint16_t)0x0200) /* Bit 1 */

#define DMA_CFG5_MSIZE                          ((uint16_t)0x0C00) /* MSIZE[1:0] bits (Memory size) */
#define DMA_CFG5_MSIZE_0                        ((uint16_t)0x0400) /* Bit 0 */
#define DMA_CFG5_MSIZE_1                        ((uint16_t)0x0800) /* Bit 1 */

#define DMA_CFG5_PL                             ((uint16_t)0x3000) /* PL[1:0] bits (Channel Priority level) */
#define DMA_CFG5_PL_0                           ((uint16_t)0x1000) /* Bit 0 */
#define DMA_CFG5_PL_1                           ((uint16_t)0x2000) /* Bit 1 */

#define DMA_CFG5_MEM2MEM                        ((uint16_t)0x4000) /* Memory to memory mode enable */

/*******************  Bit definition for DMA_CFG6 register  *******************/
#define DMA_CFG6_EN                             ((uint16_t)0x0001) /* Channel enable */
#define DMA_CFG6_TCIE                           ((uint16_t)0x0002) /* Transfer complete interrupt enable */
#define DMA_CFG6_HTIE                           ((uint16_t)0x0004) /* Half Transfer interrupt enable */
#define DMA_CFG6_TEIE                           ((uint16_t)0x0008) /* Transfer error interrupt enable */
#define DMA_CFG6_DIR                            ((uint16_t)0x0010) /* Data transfer direction */
#define DMA_CFG6_CIRC                           ((uint16_t)0x0020) /* Circular mode */
#define DMA_CFG6_PINC                           ((uint16_t)0x0040) /* Peripheral increment mode */
#define DMA_CFG6_MINC                           ((uint16_t)0x0080) /* Memory increment mode */

#define DMA_CFG6_PSIZE                          ((uint16_t)0x0300) /* PSIZE[1:0] bits (Peripheral size) */
#define DMA_CFG6_PSIZE_0                        ((uint16_t)0x0100) /* Bit 0 */
#define DMA_CFG6_PSIZE_1                        ((uint16_t)0x0200) /* Bit 1 */

#define DMA_CFG6_MSIZE                          ((uint16_t)0x0C00) /* MSIZE[1:0] bits (Memory size) */
#define DMA_CFG6_MSIZE_0                        ((uint16_t)0x0400) /* Bit 0 */
#define DMA_CFG6_MSIZE_1                        ((uint16_t)0x0800) /* Bit 1 */

#define DMA_CFG6_PL                             ((uint16_t)0x3000) /* PL[1:0] bits (Channel Priority level) */
#define DMA_CFG6_PL_0                           ((uint16_t)0x1000) /* Bit 0 */
#define DMA_CFG6_PL_1                           ((uint16_t)0x2000) /* Bit 1 */

#define DMA_CFG6_MEM2MEM                        ((uint16_t)0x4000) /* Memory to memory mode */

/*******************  Bit definition for DMA_CFG7 register  *******************/
#define DMA_CFG7_EN                             ((uint16_t)0x0001) /* Channel enable */
#define DMA_CFG7_TCIE                           ((uint16_t)0x0002) /* Transfer complete interrupt enable */
#define DMA_CFG7_HTIE                           ((uint16_t)0x0004) /* Half Transfer interrupt enable */
#define DMA_CFG7_TEIE                           ((uint16_t)0x0008) /* Transfer error interrupt enable */
#define DMA_CFG7_DIR                            ((uint16_t)0x0010) /* Data transfer direction */
#define DMA_CFG7_CIRC                           ((uint16_t)0x0020) /* Circular mode */
#define DMA_CFG7_PINC                           ((uint16_t)0x0040) /* Peripheral increment mode */
#define DMA_CFG7_MINC                           ((uint16_t)0x0080) /* Memory increment mode */

#define DMA_CFG7_PSIZE                          ((uint16_t)0x0300) /* PSIZE[1:0] bits (Peripheral size) */
#define DMA_CFG7_PSIZE_0                        ((uint16_t)0x0100) /* Bit 0 */
#define DMA_CFG7_PSIZE_1                        ((uint16_t)0x0200) /* Bit 1 */

#define DMA_CFG7_MSIZE                          ((uint16_t)0x0C00) /* MSIZE[1:0] bits (Memory size) */
#define DMA_CFG7_MSIZE_0                        ((uint16_t)0x0400) /* Bit 0 */
#define DMA_CFG7_MSIZE_1                        ((uint16_t)0x0800) /* Bit 1 */

#define DMA_CFG7_PL                             ((uint16_t)0x3000) /* PL[1:0] bits (Channel Priority level) */
#define DMA_CFG7_PL_0                           ((uint16_t)0x1000) /* Bit 0 */
#define DMA_CFG7_PL_1                           ((uint16_t)0x2000) /* Bit 1 */

#define DMA_CFG7_MEM2MEM                        ((uint16_t)0x4000) /* Memory to memory mode enable */

/******************  Bit definition for DMA_CNTR1 register  ******************/
#define DMA_CNTR1_NDT                           ((uint16_t)0xFFFF) /* Number of data to Transfer */

/******************  Bit definition for DMA_CNTR2 register  ******************/
#define DMA_CNTR2_NDT                           ((uint16_t)0xFFFF) /* Number of data to Transfer */

/******************  Bit definition for DMA_CNTR3 register  ******************/
#define DMA_CNTR3_NDT                           ((uint16_t)0xFFFF) /* Number of data to Transfer */

/******************  Bit definition for DMA_CNTR4 register  ******************/
#define DMA_CNTR4_NDT                           ((uint16_t)0xFFFF) /* Number of data to Transfer */

/******************  Bit definition for DMA_CNTR5 register  ******************/
#define DMA_CNTR5_NDT                           ((uint16_t)0xFFFF) /* Number of data to Transfer */

/******************  Bit definition for DMA_CNTR6 register  ******************/
#define DMA_CNTR6_NDT                           ((uint16_t)0xFFFF) /* Number of data to Transfer */

/******************  Bit definition for DMA_CNTR7 register  ******************/
#define DMA_CNTR7_NDT                           ((uint16_t)0xFFFF) /* Number of data to Transfer */

/******************  Bit definition for DMA_PADDR1 register  *******************/
#define DMA_PADDR1_PA                           ((uint32_t)0xFFFFFFFF) /* Peripheral Address */

/******************  Bit definition for DMA_PADDR2 register  *******************/
#define DMA_PADDR2_PA                           ((uint32_t)0xFFFFFFFF) /* Peripheral Address */

/******************  Bit definition for DMA_PADDR3 register  *******************/
#define DMA_PADDR3_PA                           ((uint32_t)0xFFFFFFFF) /* Peripheral Address */

/******************  Bit definition for DMA_PADDR4 register  *******************/
#define DMA_PADDR4_PA                           ((uint32_t)0xFFFFFFFF) /* Peripheral Address */

/******************  Bit definition for DMA_PADDR5 register  *******************/
#define DMA_PADDR5_PA                           ((uint32_t)0xFFFFFFFF) /* Peripheral Address */

/******************  Bit definition for DMA_PADDR6 register  *******************/
#define DMA_PADDR6_PA                           ((uint32_t)0xFFFFFFFF) /* Peripheral Address */

/******************  Bit definition for DMA_PADDR7 register  *******************/
#define DMA_PADDR7_PA                           ((uint32_t)0xFFFFFFFF) /* Peripheral Address */

/******************  Bit definition for DMA_MADDR1 register  *******************/
#define DMA_MADDR1_MA                           ((uint32_t)0xFFFFFFFF) /* Memory Address */

/******************  Bit definition for DMA_MADDR2 register  *******************/
#define DMA_MADDR2_MA                           ((uint32_t)0xFFFFFFFF) /* Memory Address */

/******************  Bit definition for DMA_MADDR3 register  *******************/
#define DMA_MADDR3_MA                           ((uint32_t)0xFFFFFFFF) /* Memory Address */

/******************  Bit definition for DMA_MADDR4 register  *******************/
#define DMA_MADDR4_MA                           ((uint32_t)0xFFFFFFFF) /* Memory Address */

/******************  Bit definition for DMA_MADDR5 register  *******************/
#define DMA_MADDR5_MA                           ((uint32_t)0xFFFFFFFF) /* Memory Address */

/******************  Bit definition for DMA_MADDR6 register  *******************/
#define DMA_MADDR6_MA                           ((uint32_t)0xFFFFFFFF) /* Memory Address */

/******************  Bit definition for DMA_MADDR7 register  *******************/
#define DMA_MADDR7_MA                           ((uint32_t)0xFFFFFFFF) /* Memory Address */

/******************************************************************************/
/*                    External Interrupt/Event Controller                     */
/******************************************************************************/

/*******************  Bit definition for EXTI_INTENR register  *******************/
#define EXTI_INTENR_MR0                         ((uint32_t)0x00000001) /* Interrupt Mask on line 0 */
#define EXTI_INTENR_MR1                         ((uint32_t)0x00000002) /* Interrupt Mask on line 1 */
#define EXTI_INTENR_MR2                         ((uint32_t)0x00000004) /* Interrupt Mask on line 2 */
#define EXTI_INTENR_MR3                         ((uint32_t)0x00000008) /* Interrupt Mask on line 3 */
#define EXTI_INTENR_MR4                         ((uint32_t)0x00000010) /* Interrupt Mask on line 4 */
#define EXTI_INTENR_MR5                         ((uint32_t)0x00000020) /* Interrupt Mask on line 5 */
#define EXTI_INTENR_MR6                         ((uint32_t)0x00000040) /* Interrupt Mask on line 6 */
#define EXTI_INTENR_MR7                         ((uint32_t)0x00000080) /* Interrupt Mask on line 7 */
#define EXTI_INTENR_MR8                         ((uint32_t)0x00000100) /* Interrupt Mask on line 8 */
#define EXTI_INTENR_MR9                         ((uint32_t)0x00000200) /* Interrupt Mask on line 9 */

/*******************  Bit definition for EXTI_EVENR register  *******************/
#define EXTI_EVENR_MR0                          ((uint32_t)0x00000001) /* Event Mask on line 0 */
#define EXTI_EVENR_MR1                          ((uint32_t)0x00000002) /* Event Mask on line 1 */
#define EXTI_EVENR_MR2                          ((uint32_t)0x00000004) /* Event Mask on line 2 */
#define EXTI_EVENR_MR3                          ((uint32_t)0x00000008) /* Event Mask on line 3 */
#define EXTI_EVENR_MR4                          ((uint32_t)0x00000010) /* Event Mask on line 4 */
#define EXTI_EVENR_MR5                          ((uint32_t)0x00000020) /* Event Mask on line 5 */
#define EXTI_EVENR_MR6                          ((uint32_t)0x00000040) /* Event Mask on line 6 */
#define EXTI_EVENR_MR7                          ((uint32_t)0x00000080) /* Event Mask on line 7 */
#define EXTI_EVENR_MR8                          ((uint32_t)0x00000100) /* Event Mask on line 8 */
#define EXTI_EVENR_MR9                          ((uint32_t)0x00000200) /* Event Mask on line 9 */

/******************  Bit definition for EXTI_RTENR register  *******************/
#define EXTI_RTENR_TR0                          ((uint32_t)0x00000001) /* Rising trigger event configuration bit of line 0 */
#define EXTI_RTENR_TR1                          ((uint32_t)0x00000002) /* Rising trigger event configuration bit of line 1 */
#define EXTI_RTENR_TR2                          ((uint32_t)0x00000004) /* Rising trigger event configuration bit of line 2 */
#define EXTI_RTENR_TR3                          ((uint32_t)0x00000008) /* Rising trigger event configuration bit of line 3 */
#define EXTI_RTENR_TR4                          ((uint32_t)0x00000010) /* Rising trigger event configuration bit of line 4 */
#define EXTI_RTENR_TR5                          ((uint32_t)0x00000020) /* Rising trigger event configuration bit of line 5 */
#define EXTI_RTENR_TR6                          ((uint32_t)0x00000040) /* Rising trigger event configuration bit of line 6 */
#define EXTI_RTENR_TR7                          ((uint32_t)0x00000080) /* Rising trigger event configuration bit of line 7 */
#define EXTI_RTENR_TR8                          ((uint32_t)0x00000100) /* Rising trigger event configuration bit of line 8 */
#define EXTI_RTENR_TR9                          ((uint32_t)0x00000200) /* Rising trigger event configuration bit of line 9 */

/******************  Bit definition for EXTI_FTENR register  *******************/
#define EXTI_FTENR_TR0                          ((uint32_t)0x00000001) /* Falling trigger event configuration bit of line 0 */
#define EXTI_FTENR_TR1                          ((uint32_t)0x00000002) /* Falling trigger event configuration bit of line 1 */
#define EXTI_FTENR_TR2                          ((uint32_t)0x00000004) /* Falling trigger event configuration bit of line 2 */
#define EXTI_FTENR_TR3                          ((uint32_t)0x00000008) /* Falling trigger event configuration bit of line 3 */
#define EXTI_FTENR_TR4                          ((uint32_t)0x00000010) /* Falling trigger event configuration bit of line 4 */
#define EXTI_FTENR_TR5                          ((uint32_t)0x00000020) /* Falling trigger event configuration bit of line 5 */
#define EXTI_FTENR_TR6                          ((uint32_t)0x00000040) /* Falling trigger event configuration bit of line 6 */
#define EXTI_FTENR_TR7                          ((uint32_t)0x00000080) /* Falling trigger event configuration bit of line 7 */
#define EXTI_FTENR_TR8                          ((uint32_t)0x00000100) /* Falling trigger event configuration bit of line 8 */
#define EXTI_FTENR_TR9                          ((uint32_t)0x00000200) /* Falling trigger event configuration bit of line 9 */

/******************  Bit definition for EXTI_SWIEVR register  ******************/
#define EXTI_SWIEVR_SWIEVR0                     ((uint32_t)0x00000001) /* Software Interrupt on line 0 */
#define EXTI_SWIEVR_SWIEVR1                     ((uint32_t)0x00000002) /* Software Interrupt on line 1 */
#define EXTI_SWIEVR_SWIEVR2                     ((uint32_t)0x00000004) /* Software Interrupt on line 2 */
#define EXTI_SWIEVR_SWIEVR3                     ((uint32_t)0x00000008) /* Software Interrupt on line 3 */
#define EXTI_SWIEVR_SWIEVR4                     ((uint32_t)0x00000010) /* Software Interrupt on line 4 */
#define EXTI_SWIEVR_SWIEVR5                     ((uint32_t)0x00000020) /* Software Interrupt on line 5 */
#define EXTI_SWIEVR_SWIEVR6                     ((uint32_t)0x00000040) /* Software Interrupt on line 6 */
#define EXTI_SWIEVR_SWIEVR7                     ((uint32_t)0x00000080) /* Software Interrupt on line 7 */
#define EXTI_SWIEVR_SWIEVR8                     ((uint32_t)0x00000100) /* Software Interrupt on line 8 */
#define EXTI_SWIEVR_SWIEVR9                     ((uint32_t)0x00000200) /* Software Interrupt on line 9 */

/*******************  Bit definition for EXTI_INTFR register  ********************/
#define EXTI_INTF_INTF0                         ((uint32_t)0x00000001) /* Pending bit for line 0 */
#define EXTI_INTF_INTF1                         ((uint32_t)0x00000002) /* Pending bit for line 1 */
#define EXTI_INTF_INTF2                         ((uint32_t)0x00000004) /* Pending bit for line 2 */
#define EXTI_INTF_INTF3                         ((uint32_t)0x00000008) /* Pending bit for line 3 */
#define EXTI_INTF_INTF4                         ((uint32_t)0x00000010) /* Pending bit for line 4 */
#define EXTI_INTF_INTF5                         ((uint32_t)0x00000020) /* Pending bit for line 5 */
#define EXTI_INTF_INTF6                         ((uint32_t)0x00000040) /* Pending bit for line 6 */
#define EXTI_INTF_INTF7                         ((uint32_t)0x00000080) /* Pending bit for line 7 */
#define EXTI_INTF_INTF8                         ((uint32_t)0x00000100) /* Pending bit for line 8 */
#define EXTI_INTF_INTF9                         ((uint32_t)0x00000200) /* Pending bit for line 9 */

/******************************************************************************/
/*                      FLASH and Option Bytes Registers                      */
/******************************************************************************/

/*******************  Bit definition for FLASH_ACTLR register  ******************/
#define FLASH_ACTLR_LATENCY                     ((uint8_t)0x03) /* LATENCY[2:0] bits (Latency) */
#define FLASH_ACTLR_LATENCY_0                   ((uint8_t)0x00) /* Bit 0 */
#define FLASH_ACTLR_LATENCY_1                   ((uint8_t)0x01) /* Bit 0 */
#define FLASH_ACTLR_LATENCY_2                   ((uint8_t)0x02) /* Bit 1 */

/******************  Bit definition for FLASH_KEYR register  ******************/
#define FLASH_KEYR_FKEYR                        ((uint32_t)0xFFFFFFFF) /* FPEC Key */

/*****************  Bit definition for FLASH_OBKEYR register  ****************/
#define FLASH_OBKEYR_OBKEYR                     ((uint32_t)0xFFFFFFFF) /* Option Byte Key */

/******************  Bit definition for FLASH_STATR register  *******************/
#define FLASH_STATR_BSY                         ((uint8_t)0x01) /* Busy */
#define FLASH_STATR_WRPRTERR                    ((uint8_t)0x10) /* Write Protection Error */
#define FLASH_STATR_EOP                         ((uint8_t)0x20) /* End of operation */
#define FLASH_STATR_MODE                        ((uint16_t)0x4000)
#define FLASH_STATR_LOCK                        ((uint16_t)0x8000)

/*******************  Bit definition for FLASH_CTLR register  *******************/
#define FLASH_CTLR_PG                           ((uint16_t)0x0001)     /* Programming */
#define FLASH_CTLR_PER                          ((uint16_t)0x0002)     /* Page Erase 1KByte*/
#define FLASH_CTLR_MER                          ((uint16_t)0x0004)     /* Mass Erase */
#define FLASH_CTLR_OPTPG                        ((uint16_t)0x0010)     /* Option Byte Programming */
#define FLASH_CTLR_OPTER                        ((uint16_t)0x0020)     /* Option Byte Erase */
#define FLASH_CTLR_STRT                         ((uint16_t)0x0040)     /* Start */
#define FLASH_CTLR_LOCK                         ((uint16_t)0x0080)     /* Lock */
#define FLASH_CTLR_OPTWRE                       ((uint16_t)0x0200)     /* Option Bytes Write Enable */
#define FLASH_CTLR_ERRIE                        ((uint16_t)0x0400)     /* Error Interrupt Enable */
#define FLASH_CTLR_EOPIE                        ((uint16_t)0x1000)     /* End of operation interrupt enable */
#define FLASH_CTLR_FLOCK                        ((uint16_t)0x8000)
#define FLASH_CTLR_PAGE_PG                      ((uint32_t)0x00010000) /* Page Programming 64Byte */
#define FLASH_CTLR_PAGE_ER                      ((uint32_t)0x00020000) /* Page Erase 64Byte */
#define FLASH_CTLR_BUF_LOAD                     ((uint32_t)0x00040000) /* Buffer Load */
#define FLASH_CTLR_BUF_RST                      ((uint32_t)0x00080000) /* Buffer Reset */

/*******************  Bit definition for FLASH_ADDR register  *******************/
#define FLASH_ADDR_FAR                          ((uint32_t)0xFFFFFFFF) /* Flash Address */

/******************  Bit definition for FLASH_OBR register  *******************/
#define FLASH_OBR_OPTERR                        ((uint16_t)0x0001) /* Option Byte Error */
#define FLASH_OBR_RDPRT                         ((uint16_t)0x0002) /* Read protection */

#define FLASH_OBR_USER                          ((uint16_t)0x03FC) /* User Option Bytes */
#define FLASH_OBR_WDG_SW                        ((uint16_t)0x0004) /* WDG_SW */
#define FLASH_OBR_nRST_STOP                     ((uint16_t)0x0008) 
#define FLASH_OBR_STANDY_RST                    ((uint16_t)0x0010)
#define FLASH_OBR_nRST_STDBY                    ((uint16_t)0x0010) 
#define FLASH_OBR_RST_MODE                      ((uint16_t)0x0060) /* RST_MODE */
#define FLASH_OBR_STATR_MODE                    ((uint16_t)0x0080)
#define FLASH_OBR_FIX_11                        ((uint16_t)0x0300)

/******************  Bit definition for FLASH_WPR register  ******************/
#define FLASH_WPR_WRP                           ((uint32_t)0xFFFFFFFF) /* Write Protect */

/******************  Bit definition for FLASH_RDPR register  *******************/
#define FLASH_RDPR_RDPR                         ((uint32_t)0x000000FF) /* Read protection option byte */
#define FLASH_RDPR_nRDPR                        ((uint32_t)0x0000FF00) /* Read protection complemented option byte */

/******************  Bit definition for FLASH_USER register  ******************/
#define FLASH_USER_USER                         ((uint32_t)0x00FF0000) /* User option byte */
#define FLASH_USER_nUSER                        ((uint32_t)0xFF000000) /* User complemented option byte */

/******************  Bit definition for FLASH_Data0 register  *****************/
#define FLASH_Data0_Data0                       ((uint32_t)0x000000FF) /* User data storage option byte */
#define FLASH_Data0_nData0                      ((uint32_t)0x0000FF00) /* User data storage complemented option byte */

/******************  Bit definition for FLASH_Data1 register  *****************/
#define FLASH_Data1_Data1                       ((uint32_t)0x00FF0000) /* User data storage option byte */
#define FLASH_Data1_nData1                      ((uint32_t)0xFF000000) /* User data storage complemented option byte */

/******************  Bit definition for FLASH_WRPR0 register  ******************/
#define FLASH_WRPR0_WRPR0                       ((uint32_t)0x000000FF) /* Flash memory write protection option bytes */
#define FLASH_WRPR0_nWRPR0                      ((uint32_t)0x0000FF00) /* Flash memory write protection complemented option bytes */

/******************  Bit definition for FLASH_WRPR1 register  ******************/
#define FLASH_WRPR1_WRPR1                       ((uint32_t)0x00FF0000) /* Flash memory write protection option bytes */
#define FLASH_WRPR1_nWRPR1                      ((uint32_t)0xFF000000) /* Flash memory write protection complemented option bytes */

/******************  Bit definition for FLASH_MODEKEYR register  ******************/
#define FLASH_MODEKEYR_KEY1                     ((uint32_t)0x45670123)
#define FLASH_MODEKEYR_KEY2                     ((uint32_t)0xCDEF89AB)

/******************  Bit definition for FLASH__BOOT_MODEKEYR register  ******************/
#define FLASH_BOOT_MODEKEYR_KEY1                 ((uint32_t)0x45670123)
#define FLASH_BOOT_MODEKEYR_KEY2                 ((uint32_t)0xCDEF89AB)

/******************************************************************************/
/*                General Purpose and Alternate Function I/O                  */
/******************************************************************************/

/*******************  Bit definition for GPIO_CFGLR register  *******************/
#define GPIO_CFGLR_MODE                         ((uint32_t)0x33333333) /* Port x mode bits */

#define GPIO_CFGLR_MODE0                        ((uint32_t)0x00000003) /* MODE0[1:0] bits (Port x mode bits, pin 0) */
#define GPIO_CFGLR_MODE0_0                      ((uint32_t)0x00000001) /* Bit 0 */
#define GPIO_CFGLR_MODE0_1                      ((uint32_t)0x00000002) /* Bit 1 */

#define GPIO_CFGLR_MODE1                        ((uint32_t)0x00000030) /* MODE1[1:0] bits (Port x mode bits, pin 1) */
#define GPIO_CFGLR_MODE1_0                      ((uint32_t)0x00000010) /* Bit 0 */
#define GPIO_CFGLR_MODE1_1                      ((uint32_t)0x00000020) /* Bit 1 */

#define GPIO_CFGLR_MODE2                        ((uint32_t)0x00000300) /* MODE2[1:0] bits (Port x mode bits, pin 2) */
#define GPIO_CFGLR_MODE2_0                      ((uint32_t)0x00000100) /* Bit 0 */
#define GPIO_CFGLR_MODE2_1                      ((uint32_t)0x00000200) /* Bit 1 */

#define GPIO_CFGLR_MODE3                        ((uint32_t)0x00003000) /* MODE3[1:0] bits (Port x mode bits, pin 3) */
#define GPIO_CFGLR_MODE3_0                      ((uint32_t)0x00001000) /* Bit 0 */
#define GPIO_CFGLR_MODE3_1                      ((uint32_t)0x00002000) /* Bit 1 */

#define GPIO_CFGLR_MODE4                        ((uint32_t)0x00030000) /* MODE4[1:0] bits (Port x mode bits, pin 4) */
#define GPIO_CFGLR_MODE4_0                      ((uint32_t)0x00010000) /* Bit 0 */
#define GPIO_CFGLR_MODE4_1                      ((uint32_t)0x00020000) /* Bit 1 */

#define GPIO_CFGLR_MODE5                        ((uint32_t)0x00300000) /* MODE5[1:0] bits (Port x mode bits, pin 5) */
#define GPIO_CFGLR_MODE5_0                      ((uint32_t)0x00100000) /* Bit 0 */
#define GPIO_CFGLR_MODE5_1                      ((uint32_t)0x00200000) /* Bit 1 */

#define GPIO_CFGLR_MODE6                        ((uint32_t)0x03000000) /* MODE6[1:0] bits (Port x mode bits, pin 6) */
#define GPIO_CFGLR_MODE6_0                      ((uint32_t)0x01000000) /* Bit 0 */
#define GPIO_CFGLR_MODE6_1                      ((uint32_t)0x02000000) /* Bit 1 */

#define GPIO_CFGLR_MODE7                        ((uint32_t)0x30000000) /* MODE7[1:0] bits (Port x mode bits, pin 7) */
#define GPIO_CFGLR_MODE7_0                      ((uint32_t)0x10000000) /* Bit 0 */
#define GPIO_CFGLR_MODE7_1                      ((uint32_t)0x20000000) /* Bit 1 */

#define GPIO_CFGLR_CNF                          ((uint32_t)0xCCCCCCCC) /* Port x configuration bits */

#define GPIO_CFGLR_CNF0                         ((uint32_t)0x0000000C) /* CNF0[1:0] bits (Port x configuration bits, pin 0) */
#define GPIO_CFGLR_CNF0_0                       ((uint32_t)0x00000004) /* Bit 0 */
#define GPIO_CFGLR_CNF0_1                       ((uint32_t)0x00000008) /* Bit 1 */

#define GPIO_CFGLR_CNF1                         ((uint32_t)0x000000C0) /* CNF1[1:0] bits (Port x configuration bits, pin 1) */
#define GPIO_CFGLR_CNF1_0                       ((uint32_t)0x00000040) /* Bit 0 */
#define GPIO_CFGLR_CNF1_1                       ((uint32_t)0x00000080) /* Bit 1 */

#define GPIO_CFGLR_CNF2                         ((uint32_t)0x00000C00) /* CNF2[1:0] bits (Port x configuration bits, pin 2) */
#define GPIO_CFGLR_CNF2_0                       ((uint32_t)0x00000400) /* Bit 0 */
#define GPIO_CFGLR_CNF2_1                       ((uint32_t)0x00000800) /* Bit 1 */

#define GPIO_CFGLR_CNF3                         ((uint32_t)0x0000C000) /* CNF3[1:0] bits (Port x configuration bits, pin 3) */
#define GPIO_CFGLR_CNF3_0                       ((uint32_t)0x00004000) /* Bit 0 */
#define GPIO_CFGLR_CNF3_1                       ((uint32_t)0x00008000) /* Bit 1 */

#define GPIO_CFGLR_CNF4                         ((uint32_t)0x000C0000) /* CNF4[1:0] bits (Port x configuration bits, pin 4) */
#define GPIO_CFGLR_CNF4_0                       ((uint32_t)0x00040000) /* Bit 0 */
#define GPIO_CFGLR_CNF4_1                       ((uint32_t)0x00080000) /* Bit 1 */

#define GPIO_CFGLR_CNF5                         ((uint32_t)0x00C00000) /* CNF5[1:0] bits (Port x configuration bits, pin 5) */
#define GPIO_CFGLR_CNF5_0                       ((uint32_t)0x00400000) /* Bit 0 */
#define GPIO_CFGLR_CNF5_1                       ((uint32_t)0x00800000) /* Bit 1 */

#define GPIO_CFGLR_CNF6                         ((uint32_t)0x0C000000) /* CNF6[1:0] bits (Port x configuration bits, pin 6) */
#define GPIO_CFGLR_CNF6_0                       ((uint32_t)0x04000000) /* Bit 0 */
#define GPIO_CFGLR_CNF6_1                       ((uint32_t)0x08000000) /* Bit 1 */

#define GPIO_CFGLR_CNF7                         ((uint32_t)0xC0000000) /* CNF7[1:0] bits (Port x configuration bits, pin 7) */
#define GPIO_CFGLR_CNF7_0                       ((uint32_t)0x40000000) /* Bit 0 */
#define GPIO_CFGLR_CNF7_1                       ((uint32_t)0x80000000) /* Bit 1 */

/*******************  Bit definition for GPIO_INDR register  *******************/
#define GPIO_INDR_IDR0                          ((uint16_t)0x0001) /* Port input data, bit 0 */
#define GPIO_INDR_IDR1                          ((uint16_t)0x0002) /* Port input data, bit 1 */
#define GPIO_INDR_IDR2                          ((uint16_t)0x0004) /* Port input data, bit 2 */
#define GPIO_INDR_IDR3                          ((uint16_t)0x0008) /* Port input data, bit 3 */
#define GPIO_INDR_IDR4                          ((uint16_t)0x0010) /* Port input data, bit 4 */
#define GPIO_INDR_IDR5                          ((uint16_t)0x0020) /* Port input data, bit 5 */
#define GPIO_INDR_IDR6                          ((uint16_t)0x0040) /* Port input data, bit 6 */
#define GPIO_INDR_IDR7                          ((uint16_t)0x0080) /* Port input data, bit 7 */

/*******************  Bit definition for GPIO_OUTDR register  *******************/
#define GPIO_OUTDR_ODR0                         ((uint16_t)0x0001) /* Port output data, bit 0 */
#define GPIO_OUTDR_ODR1                         ((uint16_t)0x0002) /* Port output data, bit 1 */
#define GPIO_OUTDR_ODR2                         ((uint16_t)0x0004) /* Port output data, bit 2 */
#define GPIO_OUTDR_ODR3                         ((uint16_t)0x0008) /* Port output data, bit 3 */
#define GPIO_OUTDR_ODR4                         ((uint16_t)0x0010) /* Port output data, bit 4 */
#define GPIO_OUTDR_ODR5                         ((uint16_t)0x0020) /* Port output data, bit 5 */
#define GPIO_OUTDR_ODR6                         ((uint16_t)0x0040) /* Port output data, bit 6 */
#define GPIO_OUTDR_ODR7                         ((uint16_t)0x0080) /* Port output data, bit 7 */

/******************  Bit definition for GPIO_BSHR register  *******************/
#define GPIO_BSHR_BS0                           ((uint32_t)0x00000001) /* Port x Set bit 0 */
#define GPIO_BSHR_BS1                           ((uint32_t)0x00000002) /* Port x Set bit 1 */
#define GPIO_BSHR_BS2                           ((uint32_t)0x00000004) /* Port x Set bit 2 */
#define GPIO_BSHR_BS3                           ((uint32_t)0x00000008) /* Port x Set bit 3 */
#define GPIO_BSHR_BS4                           ((uint32_t)0x00000010) /* Port x Set bit 4 */
#define GPIO_BSHR_BS5                           ((uint32_t)0x00000020) /* Port x Set bit 5 */
#define GPIO_BSHR_BS6                           ((uint32_t)0x00000040) /* Port x Set bit 6 */
#define GPIO_BSHR_BS7                           ((uint32_t)0x00000080) /* Port x Set bit 7 */

#define GPIO_BSHR_BR0                           ((uint32_t)0x00010000) /* Port x Reset bit 0 */
#define GPIO_BSHR_BR1                           ((uint32_t)0x00020000) /* Port x Reset bit 1 */
#define GPIO_BSHR_BR2                           ((uint32_t)0x00040000) /* Port x Reset bit 2 */
#define GPIO_BSHR_BR3                           ((uint32_t)0x00080000) /* Port x Reset bit 3 */
#define GPIO_BSHR_BR4                           ((uint32_t)0x00100000) /* Port x Reset bit 4 */
#define GPIO_BSHR_BR5                           ((uint32_t)0x00200000) /* Port x Reset bit 5 */
#define GPIO_BSHR_BR6                           ((uint32_t)0x00400000) /* Port x Reset bit 6 */
#define GPIO_BSHR_BR7                           ((uint32_t)0x00800000) /* Port x Reset bit 7 */

/*******************  Bit definition for GPIO_BCR register  *******************/
#define GPIO_BCR_BR0                            ((uint16_t)0x0001) /* Port x Reset bit 0 */
#define GPIO_BCR_BR1                            ((uint16_t)0x0002) /* Port x Reset bit 1 */
#define GPIO_BCR_BR2                            ((uint16_t)0x0004) /* Port x Reset bit 2 */
#define GPIO_BCR_BR3                            ((uint16_t)0x0008) /* Port x Reset bit 3 */
#define GPIO_BCR_BR4                            ((uint16_t)0x0010) /* Port x Reset bit 4 */
#define GPIO_BCR_BR5                            ((uint16_t)0x0020) /* Port x Reset bit 5 */
#define GPIO_BCR_BR6                            ((uint16_t)0x0040) /* Port x Reset bit 6 */
#define GPIO_BCR_BR7                            ((uint16_t)0x0080) /* Port x Reset bit 7 */

/******************  Bit definition for GPIO_LCKR register  *******************/
#define GPIO_LCK0                               ((uint32_t)0x00000001) /* Port x Lock bit 0 */
#define GPIO_LCK1                               ((uint32_t)0x00000002) /* Port x Lock bit 1 */
#define GPIO_LCK2                               ((uint32_t)0x00000004) /* Port x Lock bit 2 */
#define GPIO_LCK3                               ((uint32_t)0x00000008) /* Port x Lock bit 3 */
#define GPIO_LCK4                               ((uint32_t)0x00000010) /* Port x Lock bit 4 */
#define GPIO_LCK5                               ((uint32_t)0x00000020) /* Port x Lock bit 5 */
#define GPIO_LCK6                               ((uint32_t)0x00000040) /* Port x Lock bit 6 */
#define GPIO_LCK7                               ((uint32_t)0x00000080) /* Port x Lock bit 7 */
#define GPIO_LCKK                               ((uint32_t)0x00000100) 

/******************  Bit definition for AFIO_PCFR1register  *******************/
#define AFIO_PCFR1_SPI1_REMAP                   ((uint32_t)0x00000001) /* SPI1 remapping */
#define AFIO_PCFR1_I2C1_REMAP                   ((uint32_t)0x00000002) /* I2C1 remapping */
#define AFIO_PCFR1_USART1_REMAP                 ((uint32_t)0x00000004) /* USART1 remapping */

#define AFIO_PCFR1_TIM1_REMAP                   ((uint32_t)0x000000C0) /* TIM1_REMAP[1:0] bits (TIM1 remapping) */
#define AFIO_PCFR1_TIM1_REMAP_0                 ((uint32_t)0x00000040) /* Bit 0 */
#define AFIO_PCFR1_TIM1_REMAP_1                 ((uint32_t)0x00000080) /* Bit 1 */

#define AFIO_PCFR1_TIM1_REMAP_NOREMAP           ((uint32_t)0x00000000) /* No remap (ETR/PA12, CH1/PA8, CH2/PA9, CH3/PA10, CH4/PA11, BKIN/PB12, CH1N/PB13, CH2N/PB14, CH3N/PB15) */
#define AFIO_PCFR1_TIM1_REMAP_PARTIALREMAP      ((uint32_t)0x00000040) /* Partial remap (ETR/PA12, CH1/PA8, CH2/PA9, CH3/PA10, CH4/PA11, BKIN/PA6, CH1N/PA7, CH2N/PB0, CH3N/PB1) */
#define AFIO_PCFR1_TIM1_REMAP_PARTIALREMAP_1    ((uint32_t)0x00000080)
#define AFIO_PCFR1_TIM1_REMAP_FULLREMAP         ((uint32_t)0x000000C0) /* Full remap (ETR/PE7, CH1/PE9, CH2/PE11, CH3/PE13, CH4/PE14, BKIN/PE15, CH1N/PE8, CH2N/PE10, CH3N/PE12) */

#define AFIO_PCFR1_TIM2_REMAP                   ((uint32_t)0x00000300) /* TIM2_REMAP[1:0] bits (TIM2 remapping) */
#define AFIO_PCFR1_TIM2_REMAP_0                 ((uint32_t)0x00000100) /* Bit 0 */
#define AFIO_PCFR1_TIM2_REMAP_1                 ((uint32_t)0x00000200) /* Bit 1 */

#define AFIO_PCFR1_TIM2_REMAP_NOREMAP           ((uint32_t)0x00000000) /* No remap (CH1/ETR/PA0, CH2/PA1, CH3/PA2, CH4/PA3) */
#define AFIO_PCFR1_TIM2_REMAP_PARTIALREMAP1     ((uint32_t)0x00000100) /* Partial remap (CH1/ETR/PA15, CH2/PB3, CH3/PA2, CH4/PA3) */
#define AFIO_PCFR1_TIM2_REMAP_PARTIALREMAP2     ((uint32_t)0x00000200) /* Partial remap (CH1/ETR/PA0, CH2/PA1, CH3/PB10, CH4/PB11) */
#define AFIO_PCFR1_TIM2_REMAP_FULLREMAP         ((uint32_t)0x00000300) /* Full remap (CH1/ETR/PA15, CH2/PB3, CH3/PB10, CH4/PB11) */

#define AFIO_PCFR1_PA12_REMAP                   ((uint32_t)0x00008000) /* Port D0/Port D1 mapping on OSC_IN/OSC_OUT */
#define AFIO_PCFR1_ADC1_ETRGINJ_REMAP           ((uint32_t)0x00020000) /* ADC 1 External Trigger Injected Conversion remapping */
#define AFIO_PCFR1_ADC1_ETRGREG_REMAP           ((uint32_t)0x00040000) /* ADC 1 External Trigger Regular Conversion remapping */

#define AFIO_PCFR1_USART1_HIGH_BIT_REMAP        ((uint32_t)0x00200000)
#define AFIO_PCFR1_I2C1_HIGH_BIT_REMAP          ((uint32_t)0x00400000)
#define AFIO_PCFR1_TIM1_1_RM                    ((uint32_t)0x00800000)

#define AFIO_PCFR1_SWJ_CFG                      ((uint32_t)0x07000000) /* SWJ_CFG[2:0] bits (Serial Wire JTAG configuration) */
#define AFIO_PCFR1_SWJ_CFG_0                    ((uint32_t)0x01000000) /* Bit 0 */
#define AFIO_PCFR1_SWJ_CFG_1                    ((uint32_t)0x02000000) /* Bit 1 */
#define AFIO_PCFR1_SWJ_CFG_2                    ((uint32_t)0x04000000) /* Bit 2 */

#define AFIO_PCFR1_SWJ_CFG_RESET                ((uint32_t)0x00000000) 
#define AFIO_PCFR1_SWJ_CFG_NOJNTRST             ((uint32_t)0x01000000) 
#define AFIO_PCFR1_SWJ_CFG_JTAGDISABLE          ((uint32_t)0x02000000) 
#define AFIO_PCFR1_SWJ_CFG_DISABLE              ((uint32_t)0x04000000) /* JTAG-DP Disabled and SW-DP Disabled */

/*****************  Bit definition for AFIO_EXTICR1 register  *****************/
#define AFIO_EXTICR1_EXTI0                      ((uint16_t)0x0003) /* EXTI 0 configuration */
#define AFIO_EXTICR1_EXTI1                      ((uint16_t)0x000C) /* EXTI 1 configuration */
#define AFIO_EXTICR1_EXTI2                      ((uint16_t)0x0030) /* EXTI 2 configuration */
#define AFIO_EXTICR1_EXTI3                      ((uint16_t)0x00C0) /* EXTI 3 configuration */
#define AFIO_EXTICR1_EXTI4                      ((uint16_t)0x0300)
#define AFIO_EXTICR1_EXTI5                      ((uint16_t)0x0C00)
#define AFIO_EXTICR1_EXTI6                      ((uint16_t)0x3000)
#define AFIO_EXTICR1_EXTI7                      ((uint16_t)0xC000)

#define AFIO_EXTICR1_EXTI0_PA                   ((uint16_t)0x0000) /* PA[0] pin */
#define AFIO_EXTICR1_EXTI0_PC                   ((uint16_t)0x0002) /* PC[0] pin */
#define AFIO_EXTICR1_EXTI0_PD                   ((uint16_t)0x0003) /* PD[0] pin */

#define AFIO_EXTICR1_EXTI1_PA                   ((uint16_t)0x0000) /* PA[1] pin */
#define AFIO_EXTICR1_EXTI1_PC                   ((uint16_t)0x0008) /* PC[1] pin */
#define AFIO_EXTICR1_EXTI1_PD                   ((uint16_t)0x000C) /* PD[1] pin */

#define AFIO_EXTICR1_EXTI2_PA                   ((uint16_t)0x0000) /* PA[2] pin */
#define AFIO_EXTICR1_EXTI2_PC                   ((uint16_t)0x0020) /* PC[2] pin */
#define AFIO_EXTICR1_EXTI2_PD                   ((uint16_t)0x0030) /* PD[2] pin */

#define AFIO_EXTICR1_EXTI3_PA                   ((uint16_t)0x0000) /* PA[3] pin */
#define AFIO_EXTICR1_EXTI3_PC                   ((uint16_t)0x0080) /* PC[3] pin */
#define AFIO_EXTICR1_EXTI3_PD                   ((uint16_t)0x00C0) /* PD[3] pin */

#define AFIO_EXTICR1_EXTI4_PA                   ((uint16_t)0x0000) 
#define AFIO_EXTICR1_EXTI4_PC                   ((uint16_t)0x0200)
#define AFIO_EXTICR1_EXTI4_PD                   ((uint16_t)0x0300) 

#define AFIO_EXTICR1_EXTI5_PA                   ((uint16_t)0x0000) 
#define AFIO_EXTICR1_EXTI5_PC                   ((uint16_t)0x0800)
#define AFIO_EXTICR1_EXTI5_PD                   ((uint16_t)0x0C00) 

#define AFIO_EXTICR1_EXTI6_PA                   ((uint16_t)0x0000) 
#define AFIO_EXTICR1_EXTI6_PC                   ((uint16_t)0x2000)
#define AFIO_EXTICR1_EXTI6_PD                   ((uint16_t)0x3000) 

#define AFIO_EXTICR1_EXTI7_PA                   ((uint16_t)0x0000) 
#define AFIO_EXTICR1_EXTI7_PC                   ((uint16_t)0x8000)
#define AFIO_EXTICR1_EXTI7_PD                   ((uint16_t)0xC000) 

/******************************************************************************/
/*                           Independent WATCHDOG                             */
/******************************************************************************/

/*******************  Bit definition for IWDG_CTLR register  ********************/
#define IWDG_KEY                                ((uint16_t)0xFFFF) /* Key value (write only, read 0000h) */

/*******************  Bit definition for IWDG_PSCR register  ********************/
#define IWDG_PR                                 ((uint8_t)0x07) /* PR[2:0] (Prescaler divider) */
#define IWDG_PR_0                               ((uint8_t)0x01) /* Bit 0 */
#define IWDG_PR_1                               ((uint8_t)0x02) /* Bit 1 */
#define IWDG_PR_2                               ((uint8_t)0x04) /* Bit 2 */

/*******************  Bit definition for IWDG_RLDR register  *******************/
#define IWDG_RL                                 ((uint16_t)0x0FFF) /* Watchdog counter reload value */

/*******************  Bit definition for IWDG_STATR register  ********************/
#define IWDG_PVU                                ((uint8_t)0x01) /* Watchdog prescaler value update */
#define IWDG_RVU                                ((uint8_t)0x02) /* Watchdog counter reload value update */

/******************************************************************************/
/*                      Inter-integrated Circuit Interface                    */
/******************************************************************************/

/*******************  Bit definition for I2C_CTLR1 register  ********************/
#define I2C_CTLR1_PE                            ((uint16_t)0x0001) /* Peripheral Enable */
#define I2C_CTLR1_ENPEC                         ((uint16_t)0x0020) /* PEC Enable */
#define I2C_CTLR1_ENGC                          ((uint16_t)0x0040) /* General Call Enable */
#define I2C_CTLR1_NOSTRETCH                     ((uint16_t)0x0080) /* Clock Stretching Disable (Slave mode) */
#define I2C_CTLR1_START                         ((uint16_t)0x0100) /* Start Generation */
#define I2C_CTLR1_STOP                          ((uint16_t)0x0200) /* Stop Generation */
#define I2C_CTLR1_ACK                           ((uint16_t)0x0400) /* Acknowledge Enable */
#define I2C_CTLR1_POS                           ((uint16_t)0x0800) /* Acknowledge/PEC Position (for data reception) */
#define I2C_CTLR1_PEC                           ((uint16_t)0x1000) /* Packet Error Checking */
#define I2C_CTLR1_SWRST                         ((uint16_t)0x8000) /* Software Reset */

/*******************  Bit definition for I2C_CTLR2 register  ********************/
#define I2C_CTLR2_FREQ                          ((uint16_t)0x003F) /* FREQ[5:0] bits (Peripheral Clock Frequency) */
#define I2C_CTLR2_FREQ_0                        ((uint16_t)0x0001) /* Bit 0 */
#define I2C_CTLR2_FREQ_1                        ((uint16_t)0x0002) /* Bit 1 */
#define I2C_CTLR2_FREQ_2                        ((uint16_t)0x0004) /* Bit 2 */
#define I2C_CTLR2_FREQ_3                        ((uint16_t)0x0008) /* Bit 3 */
#define I2C_CTLR2_FREQ_4                        ((uint16_t)0x0010) /* Bit 4 */
#define I2C_CTLR2_FREQ_5                        ((uint16_t)0x0020) /* Bit 5 */

#define I2C_CTLR2_ITERREN                       ((uint16_t)0x0100) /* Error Interrupt Enable */
#define I2C_CTLR2_ITEVTEN                       ((uint16_t)0x0200) /* Event Interrupt Enable */
#define I2C_CTLR2_ITBUFEN                       ((uint16_t)0x0400) /* Buffer Interrupt Enable */
#define I2C_CTLR2_DMAEN                         ((uint16_t)0x0800) /* DMA Requests Enable */
#define I2C_CTLR2_LAST                          ((uint16_t)0x1000) /* DMA Last Transfer */

/*******************  Bit definition for I2C_OADDR1 register  *******************/
#define I2C_OADDR1_ADD1_7                       ((uint16_t)0x00FE) /* Interface Address */
#define I2C_OADDR1_ADD8_9                       ((uint16_t)0x0300) /* Interface Address */

#define I2C_OADDR1_ADD0                         ((uint16_t)0x0001) /* Bit 0 */
#define I2C_OADDR1_ADD1                         ((uint16_t)0x0002) /* Bit 1 */
#define I2C_OADDR1_ADD2                         ((uint16_t)0x0004) /* Bit 2 */
#define I2C_OADDR1_ADD3                         ((uint16_t)0x0008) /* Bit 3 */
#define I2C_OADDR1_ADD4                         ((uint16_t)0x0010) /* Bit 4 */
#define I2C_OADDR1_ADD5                         ((uint16_t)0x0020) /* Bit 5 */
#define I2C_OADDR1_ADD6                         ((uint16_t)0x0040) /* Bit 6 */
#define I2C_OADDR1_ADD7                         ((uint16_t)0x0080) /* Bit 7 */
#define I2C_OADDR1_ADD8                         ((uint16_t)0x0100) /* Bit 8 */
#define I2C_OADDR1_ADD9                         ((uint16_t)0x0200) /* Bit 9 */

#define I2C_OADDR1_ADDMODE                      ((uint16_t)0x8000) /* Addressing Mode (Slave mode) */

/*******************  Bit definition for I2C_OADDR2 register  *******************/
#define I2C_OADDR2_ENDUAL                       ((uint8_t)0x01) /* Dual addressing mode enable */
#define I2C_OADDR2_ADD2                         ((uint8_t)0xFE) /* Interface address */

/********************  Bit definition for I2C_DATAR register  ********************/
#define I2C_DR_DATAR                            ((uint8_t)0xFF) /* 8-bit Data Register */

/*******************  Bit definition for I2C_STAR1 register  ********************/
#define I2C_STAR1_SB                            ((uint16_t)0x0001) /* Start Bit (Master mode) */
#define I2C_STAR1_ADDR                          ((uint16_t)0x0002) /* Address sent (master mode)/matched (slave mode) */
#define I2C_STAR1_BTF                           ((uint16_t)0x0004) /* Byte Transfer Finished */
#define I2C_STAR1_ADD10                         ((uint16_t)0x0008) /* 10-bit header sent (Master mode) */
#define I2C_STAR1_STOPF                         ((uint16_t)0x0010) /* Stop detection (Slave mode) */
#define I2C_STAR1_RXNE                          ((uint16_t)0x0040) /* Data Register not Empty (receivers) */
#define I2C_STAR1_TXE                           ((uint16_t)0x0080) /* Data Register Empty (transmitters) */
#define I2C_STAR1_BERR                          ((uint16_t)0x0100) /* Bus Error */
#define I2C_STAR1_ARLO                          ((uint16_t)0x0200) /* Arbitration Lost (master mode) */
#define I2C_STAR1_AF                            ((uint16_t)0x0400) /* Acknowledge Failure */
#define I2C_STAR1_OVR                           ((uint16_t)0x0800) /* Overrun/Underrun */
#define I2C_STAR1_PECERR                        ((uint16_t)0x1000) /* PEC Error in reception */

/*******************  Bit definition for I2C_STAR2 register  ********************/
#define I2C_STAR2_MSL                           ((uint16_t)0x0001) /* Master/Slave */
#define I2C_STAR2_BUSY                          ((uint16_t)0x0002) /* Bus Busy */
#define I2C_STAR2_TRA                           ((uint16_t)0x0004) /* Transmitter/Receiver */
#define I2C_STAR2_GENCALL                       ((uint16_t)0x0010) /* General Call Address (Slave mode) */
#define I2C_STAR2_DUALF                         ((uint16_t)0x0080) /* Dual Flag (Slave mode) */
#define I2C_STAR2_PEC                           ((uint16_t)0xFF00) /* Packet Error Checking Register */

/*******************  Bit definition for I2C_CKCFGR register  ********************/
#define I2C_CKCFGR_CCR                          ((uint16_t)0x0FFF) /* Clock Control Register in Fast/Standard mode (Master mode) */
#define I2C_CKCFGR_DUTY                         ((uint16_t)0x4000) /* Fast Mode Duty Cycle */
#define I2C_CKCFGR_FS                           ((uint16_t)0x8000) /* I2C Master Mode Selection */

/******************************************************************************/
/*                             Power Control                                  */
/******************************************************************************/

/********************  Bit definition for PWR_CTLR register  ********************/
#define PWR_CTLR_PDDS                           ((uint16_t)0x0002) /* Power Down Deepsleep */
#define PWR_CTLR_PVDE                           ((uint16_t)0x0010) /* Power Voltage Detector Enable */

#define PWR_CTLR_PLS                            ((uint16_t)0x00E0) /* PLS[2:0] bits (PVD Level Selection) */
#define PWR_CTLR_PLS_0                          ((uint16_t)0x0020) /* Bit 0 */
#define PWR_CTLR_PLS_1                          ((uint16_t)0x0040) /* Bit 1 */
#define PWR_CTLR_PLS_2                          ((uint16_t)0x0080) /* Bit 2 */

#define PWR_PVDLevel_0                          ((uint16_t)0x0000)
#define PWR_PVDLevel_1                          ((uint16_t)0x0020)
#define PWR_PVDLevel_2                          ((uint16_t)0x0040)
#define PWR_PVDLevel_3                          ((uint16_t)0x0060)
#define PWR_PVDLevel_4                          ((uint16_t)0x0080)
#define PWR_PVDLevel_5                          ((uint16_t)0x00A0)
#define PWR_PVDLevel_6                          ((uint16_t)0x00C0)
#define PWR_PVDLevel_7                          ((uint16_t)0x00E0)

/*******************  Bit definition for PWR_AWUCSR register  ********************/
#define PWR_AWUCSR_AWUEN                        ((uint16_t)0x0002) 

/*******************  Bit definition for PWR_CSR register  ********************/
#define PWR_CSR_PVDO                            ((uint16_t)0x0004) /* PVD Output */

/*******************  Bit definition for PWR_AWUWR register  ********************/
#define PWR_AWUWR                               ((uint16_t)0x003F) 

/*******************  Bit definition for PWR_AWUWR register  ********************/
#define PWR_AWUPSC                              ((uint16_t)0x000F) 
#define PWR_AWUPSC_0                            ((uint16_t)0x0000)
#define PWR_AWUPSC_2                            ((uint16_t)0x0002)
#define PWR_AWUPSC_4                            ((uint16_t)0x0003)
#define PWR_AWUPSC_8                            ((uint16_t)0x0004)
#define PWR_AWUPSC_16                           ((uint16_t)0x0005)
#define PWR_AWUPSC_32                           ((uint16_t)0x0006)
#define PWR_AWUPSC_64                           ((uint16_t)0x0007)
#define PWR_AWUPSC_128                          ((uint16_t)0x0008)
#define PWR_AWUPSC_256                          ((uint16_t)0x0009)
#define PWR_AWUPSC_512                          ((uint16_t)0x000A)
#define PWR_AWUPSC_1024                         ((uint16_t)0x000B)
#define PWR_AWUPSC_2048                         ((uint16_t)0x000C)
#define PWR_AWUPSC_4096                         ((uint16_t)0x000D)
#define PWR_AWUPSC_10240                        ((uint16_t)0x000E)
#define PWR_AWUPSC_61440                        ((uint16_t)0x000F)

/******************************************************************************/
/*                         Reset and Clock Control                            */
/******************************************************************************/

/********************  Bit definition for RCC_CTLR register  ********************/
#define RCC_HSION                               ((uint32_t)0x00000001) /* Internal High Speed clock enable */
#define RCC_HSIRDY                              ((uint32_t)0x00000002) /* Internal High Speed clock ready flag */
#define RCC_HSITRIM                             ((uint32_t)0x000000F8) /* Internal High Speed clock trimming */
#define RCC_HSICAL                              ((uint32_t)0x0000FF00) /* Internal High Speed clock Calibration */
#define RCC_HSEON                               ((uint32_t)0x00010000) /* External High Speed clock enable */
#define RCC_HSERDY                              ((uint32_t)0x00020000) /* External High Speed clock ready flag */
#define RCC_HSEBYP                              ((uint32_t)0x00040000) /* External High Speed clock Bypass */
#define RCC_CSSON                               ((uint32_t)0x00080000) /* Clock Security System enable */
#define RCC_PLLON                               ((uint32_t)0x01000000) /* PLL enable */
#define RCC_PLLRDY                              ((uint32_t)0x02000000) /* PLL clock ready flag */

/*******************  Bit definition for RCC_CFGR0 register  *******************/
#define RCC_SW                                  ((uint32_t)0x00000003) /* SW[1:0] bits (System clock Switch) */
#define RCC_SW_0                                ((uint32_t)0x00000001) /* Bit 0 */
#define RCC_SW_1                                ((uint32_t)0x00000002) /* Bit 1 */

#define RCC_SW_HSI                              ((uint32_t)0x00000000) /* HSI selected as system clock */
#define RCC_SW_HSE                              ((uint32_t)0x00000001) /* HSE selected as system clock */
#define RCC_SW_PLL                              ((uint32_t)0x00000002) /* PLL selected as system clock */

#define RCC_SWS                                 ((uint32_t)0x0000000C) /* SWS[1:0] bits (System Clock Switch Status) */
#define RCC_SWS_0                               ((uint32_t)0x00000004) /* Bit 0 */
#define RCC_SWS_1                               ((uint32_t)0x00000008) /* Bit 1 */

#define RCC_SWS_HSI                             ((uint32_t)0x00000000) /* HSI oscillator used as system clock */
#define RCC_SWS_HSE                             ((uint32_t)0x00000004) /* HSE oscillator used as system clock */
#define RCC_SWS_PLL                             ((uint32_t)0x00000008) /* PLL used as system clock */

#define RCC_HPRE                                ((uint32_t)0x000000F0) /* HPRE[3:0] bits (AHB prescaler) */
#define RCC_HPRE_0                              ((uint32_t)0x00000010) /* Bit 0 */
#define RCC_HPRE_1                              ((uint32_t)0x00000020) /* Bit 1 */
#define RCC_HPRE_2                              ((uint32_t)0x00000040) /* Bit 2 */
#define RCC_HPRE_3                              ((uint32_t)0x00000080) /* Bit 3 */

#define RCC_HPRE_DIV1                           ((uint32_t)0x00000000) /* SYSCLK not divided */
#define RCC_HPRE_DIV2                           ((uint32_t)0x00000010) /* SYSCLK divided by 2 */
#define RCC_HPRE_DIV3                           ((uint32_t)0x00000020) /* SYSCLK divided by 3 */
#define RCC_HPRE_DIV4                           ((uint32_t)0x00000030) /* SYSCLK divided by 4 */
#define RCC_HPRE_DIV5                           ((uint32_t)0x00000040) /* SYSCLK divided by 5 */
#define RCC_HPRE_DIV6                           ((uint32_t)0x00000050) /* SYSCLK divided by 6 */
#define RCC_HPRE_DIV7                           ((uint32_t)0x00000060) /* SYSCLK divided by 7 */
#define RCC_HPRE_DIV8                           ((uint32_t)0x00000070) /* SYSCLK divided by 8 */
#define RCC_HPRE_DIV16                          ((uint32_t)0x000000B0) /* SYSCLK divided by 16 */
#define RCC_HPRE_DIV32                          ((uint32_t)0x000000C0) /* SYSCLK divided by 32 */
#define RCC_HPRE_DIV64                          ((uint32_t)0x000000D0) /* SYSCLK divided by 64 */
#define RCC_HPRE_DIV128                         ((uint32_t)0x000000E0) /* SYSCLK divided by 128 */
#define RCC_HPRE_DIV256                         ((uint32_t)0x000000F0) /* SYSCLK divided by 256 */

#define RCC_ADCPRE                              ((uint32_t)0x0000F800) /* ADCPRE[4:0] bits (ADC prescaler) */
#define RCC_ADCPRE_0                            ((uint32_t)0x00000800) /* Bit 0 */
#define RCC_ADCPRE_1                            ((uint32_t)0x00001000) /* Bit 1 */
#define RCC_ADCPRE_2                            ((uint32_t)0x00002000)
#define RCC_ADCPRE_3                            ((uint32_t)0x00004000)
#define RCC_ADCPRE_4                            ((uint32_t)0x00008000)

#define RCC_ADCPRE_DIV2                         ((uint32_t)0x00000000) /* PCLK2 divided by 2 */
#define RCC_ADCPRE_DIV4                         ((uint32_t)0x00004000) /* PCLK2 divided by 4 */
#define RCC_ADCPRE_DIV6                         ((uint32_t)0x00008000) /* PCLK2 divided by 6 */
#define RCC_ADCPRE_DIV8                         ((uint32_t)0x0000C000) /* PCLK2 divided by 8 */

#define RCC_PLLSRC                              ((uint32_t)0x00010000) /* PLL entry clock source */
#define RCC_PLLSRC_HSI_Mul2                     ((uint32_t)0x00000000) /* HSI clock*2 selected as PLL entry clock source */
#define RCC_PLLSRC_HSE_Mul2                     ((uint32_t)0x00010000) /* HSE clock*2 selected as PLL entry clock source */

#define RCC_CFGR0_MCO                           ((uint32_t)0x07000000) /* MCO[2:0] bits (Microcontroller Clock Output) */
#define RCC_MCO_0                               ((uint32_t)0x01000000) /* Bit 0 */
#define RCC_MCO_1                               ((uint32_t)0x02000000) /* Bit 1 */
#define RCC_MCO_2                               ((uint32_t)0x04000000) /* Bit 2 */

#define RCC_MCO_NOCLOCK                         ((uint32_t)0x00000000) /* No clock */
#define RCC_CFGR0_MCO_SYSCLK                    ((uint32_t)0x04000000) /* System clock selected as MCO source */
#define RCC_CFGR0_MCO_HSI                       ((uint32_t)0x05000000) /* HSI clock selected as MCO source */
#define RCC_CFGR0_MCO_HSE                       ((uint32_t)0x06000000) /* HSE clock selected as MCO source  */
#define RCC_CFGR0_MCO_PLL                       ((uint32_t)0x07000000) /* PLL clock divided by 2 selected as MCO source */

/*******************  Bit definition for RCC_INTR register  ********************/
#define RCC_LSIRDYF                             ((uint32_t)0x00000001) /* LSI Ready Interrupt flag */
#define RCC_HSIRDYF                             ((uint32_t)0x00000004) /* HSI Ready Interrupt flag */
#define RCC_HSERDYF                             ((uint32_t)0x00000008) /* HSE Ready Interrupt flag */
#define RCC_PLLRDYF                             ((uint32_t)0x00000010) /* PLL Ready Interrupt flag */
#define RCC_CSSF                                ((uint32_t)0x00000080) /* Clock Security System Interrupt flag */
#define RCC_LSIRDYIE                            ((uint32_t)0x00000100) /* LSI Ready Interrupt Enable */
#define RCC_HSIRDYIE                            ((uint32_t)0x00000400) /* HSI Ready Interrupt Enable */
#define RCC_HSERDYIE                            ((uint32_t)0x00000800) /* HSE Ready Interrupt Enable */
#define RCC_PLLRDYIE                            ((uint32_t)0x00001000) /* PLL Ready Interrupt Enable */
#define RCC_LSIRDYC                             ((uint32_t)0x00010000) /* LSI Ready Interrupt Clear */
#define RCC_HSIRDYC                             ((uint32_t)0x00040000) /* HSI Ready Interrupt Clear */
#define RCC_HSERDYC                             ((uint32_t)0x00080000) /* HSE Ready Interrupt Clear */
#define RCC_PLLRDYC                             ((uint32_t)0x00100000) /* PLL Ready Interrupt Clear */
#define RCC_CSSC                                ((uint32_t)0x00800000) /* Clock Security System Interrupt Clear */

/*****************  Bit definition for RCC_APB2PRSTR register  *****************/
#define RCC_AFIORST                             ((uint32_t)0x00000001) /* Alternate Function I/O reset */
#define RCC_IOPARST                             ((uint32_t)0x00000004) /* I/O port A reset */
#define RCC_IOPCRST                             ((uint32_t)0x00000010) /* I/O port C reset */
#define RCC_IOPDRST                             ((uint32_t)0x00000020) /* I/O port D reset */
#define RCC_ADC1RST                             ((uint32_t)0x00000200) /* ADC 1 interface reset */

#define RCC_TIM1RST                             ((uint32_t)0x00000800) /* TIM1 Timer reset */
#define RCC_SPI1RST                             ((uint32_t)0x00001000) /* SPI 1 reset */
#define RCC_USART1RST                           ((uint32_t)0x00004000) /* USART1 reset */

/*****************  Bit definition for RCC_APB1PRSTR register  *****************/
#define RCC_TIM2RST                             ((uint32_t)0x00000001) /* Timer 2 reset */
#define RCC_WWDGRST                             ((uint32_t)0x00000800) /* Window Watchdog reset */
#define RCC_I2C1RST                             ((uint32_t)0x00200000) /* I2C 1 reset */

#define RCC_PWRRST                              ((uint32_t)0x10000000) /* Power interface reset */

/******************  Bit definition for RCC_AHBPCENR register  ******************/
#define RCC_DMA1EN                              ((uint16_t)0x0001) /* DMA1 clock enable */
#define RCC_SRAMEN                              ((uint16_t)0x0004) /* SRAM interface clock enable */

/******************  Bit definition for RCC_APB2PCENR register  *****************/
#define RCC_AFIOEN                              ((uint32_t)0x00000001) /* Alternate Function I/O clock enable */
#define RCC_IOPAEN                              ((uint32_t)0x00000004) /* I/O port A clock enable */
#define RCC_IOPCEN                              ((uint32_t)0x00000010) /* I/O port C clock enable */
#define RCC_IOPDEN                              ((uint32_t)0x00000020) /* I/O port D clock enable */
#define RCC_ADC1EN                              ((uint32_t)0x00000200) /* ADC 1 interface clock enable */

#define RCC_TIM1EN                              ((uint32_t)0x00000800) /* TIM1 Timer clock enable */
#define RCC_SPI1EN                              ((uint32_t)0x00001000) /* SPI 1 clock enable */
#define RCC_USART1EN                            ((uint32_t)0x00004000) /* USART1 clock enable */

/*****************  Bit definition for RCC_APB1PCENR register  ******************/
#define RCC_TIM2EN                              ((uint32_t)0x00000001) /* Timer 2 clock enabled*/
#define RCC_WWDGEN                              ((uint32_t)0x00000800) /* Window Watchdog clock enable */
#define RCC_I2C1EN                              ((uint32_t)0x00200000) /* I2C 1 clock enable */

#define RCC_PWREN                               ((uint32_t)0x10000000) /* Power interface clock enable */

/*******************  Bit definition for RCC_RSTSCKR register  ********************/
#define RCC_LSION                               ((uint32_t)0x00000001) /* Internal Low Speed oscillator enable */
#define RCC_LSIRDY                              ((uint32_t)0x00000002) /* Internal Low Speed oscillator Ready */
#define RCC_RMVF                                ((uint32_t)0x01000000) /* Remove reset flag */
#define RCC_PINRSTF                             ((uint32_t)0x04000000) /* PIN reset flag */
#define RCC_PORRSTF                             ((uint32_t)0x08000000) /* POR/PDR reset flag */
#define RCC_SFTRSTF                             ((uint32_t)0x10000000) /* Software Reset flag */
#define RCC_IWDGRSTF                            ((uint32_t)0x20000000) /* Independent Watchdog reset flag */
#define RCC_WWDGRSTF                            ((uint32_t)0x40000000) /* Window watchdog reset flag */
#define RCC_LPWRRSTF                            ((uint32_t)0x80000000) /* Low-Power reset flag */

/******************************************************************************/
/*                        Serial Peripheral Interface                         */
/******************************************************************************/

/*******************  Bit definition for SPI_CTLR1 register  ********************/
#define SPI_CTLR1_CPHA                          ((uint16_t)0x0001) /* Clock Phase */
#define SPI_CTLR1_CPOL                          ((uint16_t)0x0002) /* Clock Polarity */
#define SPI_CTLR1_MSTR                          ((uint16_t)0x0004) /* Master Selection */

#define SPI_CTLR1_BR                            ((uint16_t)0x0038) /* BR[2:0] bits (Baud Rate Control) */
#define SPI_CTLR1_BR_0                          ((uint16_t)0x0008) /* Bit 0 */
#define SPI_CTLR1_BR_1                          ((uint16_t)0x0010) /* Bit 1 */
#define SPI_CTLR1_BR_2                          ((uint16_t)0x0020) /* Bit 2 */

#define SPI_CTLR1_SPE                           ((uint16_t)0x0040) /* SPI Enable */
#define SPI_CTLR1_LSBFIRST                      ((uint16_t)0x0080)
#define SPI_CTLR1_SSI                           ((uint16_t)0x0100) /* Internal slave select */
#define SPI_CTLR1_SSM                           ((uint16_t)0x0200) /* Software slave management */
#define SPI_CTLR1_RXONLY                        ((uint16_t)0x0400) /* Receive only */
#define SPI_CTLR1_DFF                           ((uint16_t)0x0800) /* Data Frame Format */
#define SPI_CTLR1_CRCNEXT                       ((uint16_t)0x1000) /* Transmit CRC next */
#define SPI_CTLR1_CRCEN                         ((uint16_t)0x2000) /* Hardware CRC calculation enable */
#define SPI_CTLR1_BIDIOE                        ((uint16_t)0x4000) /* Output enable in bidirectional mode */
#define SPI_CTLR1_BIDIMODE                      ((uint16_t)0x8000) /* Bidirectional data mode enable */

/*******************  Bit definition for SPI_CTLR2 register  ********************/
#define SPI_CTLR2_RXDMAEN                       ((uint8_t)0x01) /* Rx Buffer DMA Enable */
#define SPI_CTLR2_TXDMAEN                       ((uint8_t)0x02) /* Tx Buffer DMA Enable */
#define SPI_CTLR2_SSOE                          ((uint8_t)0x04) /* SS Output Enable */
#define SPI_CTLR2_ERRIE                         ((uint8_t)0x20) /* Error Interrupt Enable */
#define SPI_CTLR2_RXNEIE                        ((uint8_t)0x40) /* RX buffer Not Empty Interrupt Enable */
#define SPI_CTLR2_TXEIE                         ((uint8_t)0x80) /* Tx buffer Empty Interrupt Enable */

/********************  Bit definition for SPI_STATR register  ********************/
#define SPI_STATR_RXNE                          ((uint8_t)0x01) /* Receive buffer Not Empty */
#define SPI_STATR_TXE                           ((uint8_t)0x02) /* Transmit buffer Empty */
#define SPI_STATR_CHSIDE                        ((uint8_t)0x04) /* Channel side */
#define SPI_STATR_UDR                           ((uint8_t)0x08) /* Underrun flag */
#define SPI_STATR_CRCERR                        ((uint8_t)0x10) /* CRC Error flag */
#define SPI_STATR_MODF                          ((uint8_t)0x20) /* Mode fault */
#define SPI_STATR_OVR                           ((uint8_t)0x40) /* Overrun flag */
#define SPI_STATR_BSY                           ((uint8_t)0x80) /* Busy flag */

/********************  Bit definition for SPI_DATAR register  ********************/
#define SPI_DATAR_DR                            ((uint16_t)0xFFFF) /* Data Register */

/*******************  Bit definition for SPI_CRCR register  ******************/
#define SPI_CRCR_CRCPOLY                        ((uint16_t)0xFFFF) /* CRC polynomial register */

/******************  Bit definition for SPI_RCRCR register  ******************/
#define SPI_RCRCR_RXCRC                         ((uint16_t)0xFFFF) /* Rx CRC Register */

/******************  Bit definition for SPI_TCRCR register  ******************/
#define SPI_TCRCR_TXCRC                         ((uint16_t)0xFFFF) /* Tx CRC Register */
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
