bestlaohe/newmsg/screen/page.c

/*
 * page.c
 *
 *  Created on: 2024年9月21日
 *      Author: 12630
 */
#include "page.h"
#include <string.h>
#define MAX_LINE_TO_SHOW 5                                                             // 最大显示行数
#define EDGE 1                                                                         // 边缘
#define OPERATE_DOWN 20                                                                // 操作界面下边缘
#define CHAT_DOWN 127                                                                  // 输入框下边缘
#define COLUMN ((LCD_WIDTH - EDGE - EDGE) / Font_WIDTH)                                // 行个数18
#define CHAT_HISTORY_DOWN (MAX_LINE_TO_SHOW * Font_HEIGH) + OPERATE_DOWN + EDGE + EDGE // 聊天记录下边缘5行90/18=5*12=60
#define CHAT_UP CHAT_HISTORY_DOWN + 2                                                  // 输入栏的上部分
#define CHAR_HEIGHT 18                                                                 // 单个字符高度
#define Y_OFFSET 22                                                                    // 设置页面初始的y轴偏移
int8_t Englishcount = 0;                                                               // 字符的位号
u8 Englishposx = 0;                                                                   // x的个数
u8 Englishposy = 0;                                                                   // y的个数
u8 lora_send_buf[54];                                                                  // 只有3行可以输入一行18
u8 current_setting = 0;                                                               // 当前设置的行
u8 refreshState = 1;                                                                  // 内容刷新标志位
u8 isFirstSettingShow = 1;                                                            // 设置刷新标志
u8 isFirstBattaryShow = 1;                                                            // 电池刷新标志
u8 current_line = 0;                                                                  // 当前显示的起始行
u8 total_lines = 0;                                                                   // 总的聊天记录行数

Setting settings[SETTING_COUNT] = {
    {"light", (u8 *)&TIM1->CH3CVR, NULL},
    {"shake", &shake_mode, NULL},
    {"freq", &Lora_Freq, SX1278_Init},
    {"power", &Lora_Power, SX1278_Init},
    {"lorabw", &Lora_BandWide, SX1278_Init},
    {"lorasf", &Lora_SpreadFactor, SX1278_Init}};

Page page = PAGE_SEND;

void handle_chat_event(sFONT *Font)
{
  // 处理滚动状态
  if (encode.state == ENCODE_EVENT_UP)
  {
    Englishcount = (Englishcount + 1) % 27; // 循环计数
  }
  else if (encode.state == ENCODE_EVENT_DOWN)
  {
    Englishcount = (Englishcount - 1 + 27) % 27; // 循环计数
  }

  if (lora_receive_flag == 2) // 无限等待接收回应
  {
    SX1278_LoRaTxPacket(lora_send_buf, Englishposx + Englishposy * (LCD_HEIGHT / Font->Width));
  }

  // 发送数据
  if (key.state == KEY_STATE_HOLD)
  {
    if (encode.state == ENCODE_EVENT_UP)
    {
      refreshState = 1;
      DEBUG_PRINT("start lora send\r\n");
      lora_receive_flag = 2;
      if (!SX1278_LoRaTxPacket(lora_send_buf, Englishposx + Englishposy * (LCD_HEIGHT / Font->Width)))
      {
        DEBUG_PRINT("lora send ok\r\n");
        SX1278_LoRaEntryRx(); // 进入接收模式
      }
      // 清空一切
      Englishposy = 0; // 重置行位置
      Englishposx = 0; // 重置行位置
      memset(lora_send_buf, 0, sizeof(lora_send_buf));

      LCD_0IN85_Clear(EDGE, CHAT_UP + EDGE, 127 - EDGE, 127 - EDGE, MY_THEME_BACK_COLOR); // 清除输入内容

      key.enable = 0; // 禁用键
    }
    else if (encode.state == ENCODE_EVENT_DOWN)
    {
      refreshState = 1;
      // 输入回退
      if (--Englishposx < 0)
      {
        if (Englishposy > 0)
        {
          Englishposy--;
          Englishposx = (LCD_WIDTH) / Font->Width - Font->Width; // 重置列位置
        }
        else
        {
          Englishposx = 0;
        }
      }
      key.enable = 0; // 禁用键
    }
  }

  // 确认输入
  if (key.event == KEY_EVENT_CLICK)
  {
    refreshState = 1;
    lora_send_buf[Englishposx + Englishposy * (LCD_WIDTH / Font->Width)] = 'a' + Englishcount;
    Englishposx++;
    // DEBUG_PRINT("我111的数字=%d \r\n", EDGE + EDGE + Englishposx * Font->Width);

    if (EDGE + EDGE + (Englishposx + 1) * Font->Width > LCD_WIDTH)
    {
      Englishposx = 0;
      Englishposy++;
      //  DEBUG_PRINT("我的数字=%d \r\n", CHAT_UP + EDGE + Englishposy * Font->Height);
      if (CHAT_UP + EDGE + ((Englishposy + 1) * Font->Height) >= LCD_HEIGHT)
      {
        Englishposy = 0; // 重置行位置
      }
    }
    Englishcount = 0; // 重置计数
  }
}

void handle_chat_history_event()
{
  if (encode.state == ENCODE_EVENT_UP) // 向上滚动
  {
    if (current_line > 0)
    {
      current_line--;
      refreshState = 1;
    }
  }

  if (encode.state == ENCODE_EVENT_DOWN) // 向下滚动
  {
    if (current_line < total_lines - MAX_LINE_TO_SHOW - 1)
    {
      current_line++;
      refreshState = 1;
    }
  }

  if (key.state == KEY_STATE_HOLD) // 删除聊天记录
  {
    if (encode.state == ENCODE_EVENT_DOWN)
    {
      refreshState = 1;
      memset(lora_receive_buf, 0, sizeof(lora_receive_len));                                             // 清空聊天记录
      LCD_0IN85_Clear(EDGE, OPERATE_DOWN + EDGE, 127 - EDGE, CHAT_HISTORY_DOWN - EDGE, MY_SCREEN_COLOR); // 清空显示区域

      total_lines = 0;
      current_line = 0;
      key.enable = 0; // 禁用键
    }
  }
}

// 1行18个
void show_history_data(sFONT *Font)
{

  int start_line = current_line;
  int end_line = current_line + MAX_LINE_TO_SHOW;

  // strcpy(lora_receive_buf, \
// "aelloworldthisisat" \
// "bstanotherlinewwwr" \
// "celloworldthisisat" \
// "dstanotherlinewwwr" \
// "eelloworldthisisat" \
// "fstanotherlinewwwr" \
// "gelloworldthisisat" \
// "hstanotherlinewwwr");
  //   lora_receive_len = 145;

  total_lines = (lora_receive_len + COLUMN - 1) / COLUMN; // 计算总行数

  if (end_line > total_lines)
  {
    end_line = total_lines;
  }

  // 清空显示区域
  //   LCD_0IN85_Clear(EDGE, OPERATE_DOWN + EDGE, 127 - EDGE, CHAT_HISTORY_DOWN - EDGE, MY_SCREEN_COLOR); // 清除聊天内容

  // 动态解析 lora_receive_buf 并显示当前范围内的聊天记录
  const char *ptr = lora_receive_buf;
  int line_count = 0;
  int displayed_lines = 0;
  int line_length = 0; // 每一行的长度

  while (*ptr && line_count < total_lines)
  {
    if (line_count >= start_line && line_count < end_line)
    {
      char line[COLUMN + 1] = {0};
      int i = 0;
      while (*ptr && line_length < COLUMN)
      {
        line[i++] = *ptr++;
        line_length++;
      }
      Paint_DrawString(1, 22 + (displayed_lines++) * Font->Height, line, Font, MY_THEME_BACK_COLOR, MY_THEME_COMPONT_COLOR, 'a' - 1);
    }
    else
    {
      while (*ptr && line_length < COLUMN) // 拿来跳过开头的内容用
      {
        ptr++;
        line_length++;
      }
    }
    line_count++;
    line_length = 0;
  }
}

void chat_page(sFONT *Font)
{

  show_battery(BATTERY_X, BATTERY_Y, MY_THEME_BACK_COLOR, MY_THEME_COMPONT_COLOR, &isFirstBattaryShow); // 显示电池信息

  if (refreshState)
  {
    Paint_DrawChar(1, 1, 0, &Font16_Operate, MY_THEME_BACK_COLOR, MY_THEME_COMPONT_COLOR, 0); // 设置的图标
    LCD_0IN85_Clear(0, OPERATE_DOWN, 127, CHAT_HISTORY_DOWN, MY_SCREEN_COLOR);                // 聊天记录界面
    LCD_0IN85_Clear(0, CHAT_UP, 127, CHAT_DOWN, MY_SCREEN_COLOR);                             // 输入框
    Paint_DrawRectangle(0, CHAT_UP, 127, CHAT_DOWN, GREEN, DOT_PIXEL_1X1, DRAW_FILL_EMPTY);   // 输入框高亮

    refreshState = 0;
  }

  // 绘制字符
  Paint_DrawChar(EDGE + Englishposx * Font->Width, CHAT_UP + EDGE + Englishposy * Font->Height, 'a' + Englishcount, Font, MY_THEME_BACK_COLOR, MY_THEME_COMPONT_COLOR, 'a');
  Paint_DrawString(EDGE, CHAT_UP + EDGE, lora_send_buf, Font, MY_THEME_BACK_COLOR, MY_THEME_COMPONT_COLOR, 'a');

  show_history_data(Font);
  handle_chat_event(Font);
}
void chat_history_page(sFONT *Font)
{
  show_battery(BATTERY_X, BATTERY_Y, MY_THEME_BACK_COLOR, MY_THEME_COMPONT_COLOR, &isFirstBattaryShow);
  if (refreshState)
  {
    Paint_DrawRectangle(0, OPERATE_DOWN, 127, CHAT_HISTORY_DOWN, GREEN, DOT_PIXEL_1X1, DRAW_FILL_EMPTY); // 聊天记录界面高亮
  //  LCD_0IN85_Clear(0, CHAT_UP, 128, CHAT_DOWN, MY_SCREEN_COLOR);                                        // 输入框
    Paint_DrawRectangle(0, CHAT_UP, 127, CHAT_DOWN, MY_SCREEN_COLOR, DOT_PIXEL_1X1, DRAW_FILL_EMPTY);   // 输入框高亮
    show_history_data(Font);
    refreshState = 0;
  }

  handle_chat_history_event();
}

void perpare_setting_page(sFONT *Font)
{
  show_battery(BATTERY_X, BATTERY_Y, MY_THEME_BACK_COLOR, MY_THEME_COMPONT_COLOR, &isFirstBattaryShow); // 电池组件
  if (refreshState)
  {
    LCD_0IN85_Clear(0, OPERATE_DOWN, 128, CHAT_HISTORY_DOWN, MY_SCREEN_COLOR); // 聊天记录界面
    Paint_DrawChar(0, 0, 0, &Font16_Operate, GREEN, BLUE, 0);                  // 设置页面高亮
    show_history_data(Font);
    refreshState = 0;
  }
}

/**************************************设置页面**************************************************** */
void clamp_value(int *value, int min, int max)
{
  if (*value < min)
    *value = min;
  if (*value > max)
    *value = max;
}

void update_setting_value(int value, int min, int max, int current_setting)
{
  clamp_value(&value, min, max);
  *settings[current_setting].value = (u8)value;
}

void update_current_setting(int value)
{
  switch (current_setting)
  {
  case SETTING_SCREEN_LIGHT:
    value = (value < 0) ? 0 : (value > 100) ? 100
                                            : value;
    TIM1->CH3CVR = value;
    break;
  case SETTING_SHAKE_MODE:
    *settings[current_setting].value = !(*settings[current_setting].value);
    break;
  case SETTING_LORA_FREQ:
    update_setting_value(value, LORAFREQ_MIN, LORAFREQ_MAX, current_setting);
    break;
  case SETTING_LORA_POWER:
    update_setting_value(value, LORAPOWER_MIN, LORAPOWER_MAX, current_setting);
    break;
  case SETTING_LORA_BANDWIDTH:
    update_setting_value(value, LORABANDWIDTH_MIN, LORABANDWIDTH_MAX, current_setting);
    break;
  case SETTING_LORA_SPREAD_FACTOR:
    update_setting_value(value, LORASpreadFactor_MIN, LORASpreadFactor_MAX, current_setting);
    break;
  default:
    break;
  }

  if (settings[current_setting].update_func)
  {
    settings[current_setting].update_func();
  }
}

void draw_setting(int index, int highlight, sFONT *Font)
{

  char strBuf[4]; // 用于存储最多3位数字和一个终止符
  UWORD bg_color = highlight ? GREEN : MY_THEME_COMPONT_COLOR;

  Paint_DrawString(0, index * CHAR_HEIGHT + Y_OFFSET, settings[index].name, Font, MY_THEME_BACK_COLOR, bg_color, 'a');
  Paint_DrawChar(Font->Width * strlen(settings[index].name), index * CHAR_HEIGHT + Y_OFFSET, 11, &Font16_Num, MY_THEME_BACK_COLOR, bg_color, 0);

  // 根据当前设置类型绘制值
  if (index == SETTING_SHAKE_MODE)
  {

    if (highlight || isFirstSettingShow)
    {
      isFirstSettingShow = 0;
      if (*settings[index].value == ON)
      {
        Paint_DrawString(Font->Width * (strlen(settings[index].name) + 1), index * CHAR_HEIGHT + Y_OFFSET, "0", &Font16_button, MY_THEME_BACK_COLOR, GREEN, '0');
        Paint_DrawString(Font->Width * (strlen(settings[index].name) + 1) + 15, index * CHAR_HEIGHT + Y_OFFSET + 2, "0", &Font16_cycle, GREEN, WHITE, '0');
      }
      else
      {
        Paint_DrawString(Font->Width * (strlen(settings[index].name) + 1), index * CHAR_HEIGHT + Y_OFFSET, "0", &Font16_button, MY_THEME_BACK_COLOR, RED, '0');
        Paint_DrawString((Font->Width * (strlen(settings[index].name) + 1)) + 2, index * CHAR_HEIGHT + Y_OFFSET + 2, "0", &Font16_cycle, RED, WHITE, '0');
      }
    }

    return;
  }
  else
  {
    intToStr(*settings[index].value, strBuf, 3);
  }

  Paint_DrawString(Font->Width * (strlen(settings[index].name) + 1), index * CHAR_HEIGHT + Y_OFFSET, strBuf, &Font16_Num, MY_THEME_BACK_COLOR, bg_color, '0');
}

void display_settings(sFONT *Font)
{

  if (refreshState)
  {
    for (int i = 0; i < SETTING_COUNT; i++)
    {
      draw_setting(i, i == current_setting, Font);
    }
    refreshState = 0;
  }
}

void handle_setting_event()
{
  if (encode.state == ENCODE_EVENT_UP)
  { // 编码器向上滚动
    update_current_setting(*settings[current_setting].value + 1);
    refreshState = 1;
  }
  else if (encode.state == ENCODE_EVENT_DOWN)
  { // 编码器向下滚动
    update_current_setting(*settings[current_setting].value - 1);
    refreshState = 1;
  }
  if (key.event == KEY_EVENT_CLICK)
  { // 确认键点击
    current_setting = (current_setting + 1) % SETTING_COUNT;
    refreshState = 1;
  }
}

void setting_page(sFONT *Font)
{
//设置二字
  Paint_DrawString(48, 0, "01", &Font16_setting, MY_THEME_BACK_COLOR, MY_THEME_COMPONT_COLOR, '0');

  display_settings(Font);
  handle_setting_event();
}

/**************************************设置页面**************************************************** */

void show_info(int posx, int posy, const char *label, int value, int offset)
{
  char strBuf[4];                                                                                    // 存储最多3位数字和一个终止符
  Paint_DrawString(posx, posy, label, &Font16_En, MY_THEME_BACK_COLOR, MY_THEME_COMPONT_COLOR, 'a'); // 绘制标签
  Paint_DrawChar(posx + Font16_En.Width * (offset - 1), posy, 11, &Font16_Num, MY_THEME_BACK_COLOR, MY_THEME_COMPONT_COLOR, 0);
  intToStr(value, strBuf, 3);
  Paint_DrawString(posx + Font16_Num.Width * offset, posy, strBuf, &Font16_Num, MY_THEME_BACK_COLOR, MY_THEME_COMPONT_COLOR, '0'); // 绘制值
}

void info_page()
{

  show_info(0, 0, "batadc", Battery_ADC_Average, 7);              // 调用显示电池信息
  show_info(0, 20, "rssi", SX1278_LoRaReadRSSI(), 5);             // 调用显示 Lora RSSI
  show_info(0, 40, "loraid", SX1278_Read_Reg(REG_LR_VERSION), 7); // 调用显示 Lora ID
  show_info(0, 60, "light", TIM1->CH3CVR, 6);                     // 调用显示屏幕亮度
}

void show_page()
{

  //  page = PAGE_SEND;
  switch (page) // 处理页面
  {
  case PAGE_SEND: // 发送界面
    chat_page(&Font12_En);
    if (key.event == KEY_EVENT_LONG_CLICK) // 返回
    {
      refreshState = 1;
      page = PAGE_HISTROY_CHAT;
    }
    break;

  case PAGE_HISTROY_CHAT: // 聊天记录界面  需要滚动查看记录
    chat_history_page(&Font12_En);
    if (key.event == KEY_EVENT_LONG_CLICK)
    {
      refreshState = 1;
      page = PAGE_PERPARE_SETTING;
    }

    break;

  case PAGE_PERPARE_SETTING: // 准备设置界面
    perpare_setting_page(&Font12_En);
    if (key.event == KEY_EVENT_CLICK)
    {
      refreshState = 1;
      LCD_0IN85_Clear(0, 0, 127, 127, MY_THEME_BACK_COLOR);

      // // 这是一个播放设置的地方
      // Paint_DrawChar(40, 40, 0, &Font24_icon, MY_THEME_BACK_COLOR, BLUE, 0);
      // Delay_Ms(500);
      // // 考虑删掉

      // LCD_0IN85_Clear(0, 0, 127, 127, MY_THEME_BACK_COLOR);
      isFirstSettingShow = 1;
      page = PAGE_SETTING;
    }

    if (key.event == KEY_EVENT_LONG_CLICK)
    {
      refreshState = 1;
      LCD_0IN85_Clear(0, 0, 127, 127, MY_THEME_BACK_COLOR);

      isFirstBattaryShow = 1;
      page = PAGE_SEND;
    }
    break;

  case PAGE_SETTING: // 设置界面
   // setting_page(&Font16_En);
    if (key.event == KEY_EVENT_LONG_CLICK)
    {
      refreshState = 1;
      LCD_0IN85_Clear(0, 0, 127, 127, MY_THEME_BACK_COLOR);
      // page = PAGE_INFO;
      isFirstBattaryShow = 1;
      page = PAGE_SEND;
    }
    break;

    // case PAGE_INFO: // 信息界面
    //   info_page();
    //   if (key.event == KEY_EVENT_LONG_CLICK)
    //   {
    //     LCD_0IN85_Clear(0,0,128,128,MY_THEME_BACK_COLOR);
    //     page = PAGE_SEND;
    //   }
    //   break;

  default: // 默认情况
    page = PAGE_SEND;
    break;
  }

  // 处理完事件后清除事件
  key.event = KEY_EVENT_NONE;
  encode.state = ENCODE_EVENT_NONE;
}

// 重写部分结构-
// 每个page的页面内容显示
// 每个页面的操作
// show_page显示总的page流程

// 界面显示
// 逻辑处理
