bestlaohe/newmsg/encode/encode.c

/*
 * encode.c
 *
 *  Created on: 2024年9月1日
 *      Author: 12630
 */

/**
 * @note
 * Encoder rourine
 * The main function initializes and tests an encoder, and continuously prints the encoder position and
 * speed.
 */
#include "debug.h"
#include "encode.h"
#include "SX1278.h"

u8 precnt = 0;
u8 precircle = 0;
void Encoder_Scan()
{

  if (precircle != circle || (precnt != TIM2->CNT)) // 有变化就动   140字节
  {
    if (precircle * 12 + precnt > circle * 12 + TIM2->CNT)
    {
      encode.state = ENCODE_EVENT_DOWN;
      // DEBUG_PRINT("向上");
    }
    encode.state = ENCODE_EVENT_UP;
    if (precircle * 12 + precnt < circle * 12 + TIM2->CNT)
    {
      encode.state = ENCODE_EVENT_DOWN;
      // DEBUG_PRINT("向下");
    }

    // DEBUG_PRINT("precircle*12+precnt= %d circle*12+TIM2->CNT %d step\r\n", precircle * 12 + precnt, circle * 12 + TIM2->CNT);
    // DEBUG_PRINT("Encoder position= %d circle %d step\r\n", TIM2->CNT, circle);
    precircle = circle;
    precnt = TIM2->CNT;

     refresh_SleepCounter(0); // 刷新休眠时间
    MOTOR_SET(1);
    Delay_Ms(50);
    MOTOR_SET(0);
  }
}
void Encoder_Init(u16 arr, u16 psc)
{
  TIM2_Init(arr, psc); // 自动重装载值（ARR）和预分频器（PSC）
}
/*********************************************************************
 * @fn      KEY_PRESS
 *
 * @brief   Key processing funcation.
 *
 * @return  0 - Press the key.（pd2）
 *          1 - Release Key.
 */
u8 KEY_PRESS(void)
{
  if (KEY0 == 1)
  {
    Delay_Ms(10);
    if (KEY0 == 1)
      return 1;
    else
      return 0;
  }

  return 0;
}
