bestlaohe/newmsg/encode/encode.h

/*
 * encode.h
 *
 *  Created on: 2024��9��1��
 *      Author: 12630
 */

#ifndef ENCODE_ENCODE_H_
#define ENCODE_ENCODE_H_
#include "time_app.h"
extern Encode encode;
extern volatile int circle;

void Encoder_Init(u16 arr, u16 psc);
u8 KEY_PRESS(void);
void Encoder_Scan();
#endif /* ENCODE_ENCODE_H_ */
